tangybbq/keyboard/mesa2/thumb-1to1.pdf

## mesa2 - thumb angle and reach, LEFT hand, hand-local

100.0 mm - print at 100%, no fit-to-page

Within a row only the ANGLE of the line through the two thumb keys changes.
Between rows only the REACH changes. The index column is redrawn in each cell so the distance from finger to thumb is identical across a row - register your index on it every time. Lay the thumb across a pair: the right one is reached without moving the wrist and lands square on both keys. If none fits, use measure-blank.svg - sweep and tap 4-5 dots on the arc.

### reach as V1

-15 deg | +0 deg | +15 deg

### reach 8 mm further from the fingers

-15 deg | +0 deg | +15 deg
