tangybbq/keyboard/mesa2/variants-1to1.pdf

## mesa2 - finger variants, LEFT hand, hand-local (unibody angle removed)

100.0 mm - print at 100%, no fit-to-page

Columns are anchored and splayed about their CENTRE - the point the finger rests on between the two keys - not about either key. Rest a finger on the ridge between a column's two caps. Both are chouchou with your corrections applied, bracketing the amount: spread down, pinky and index staggered toward the palm, pinky rotated harder. 1u caps. Thumb pairs are placeholders -
use thumb-1to1 for those. You already have chouchou printed; compare against that.

### V1 modest spread 19.0/19.5/21.0 stagger 24.0/6.8/0/12.0 splay +21/+5/0/-5 rock 17

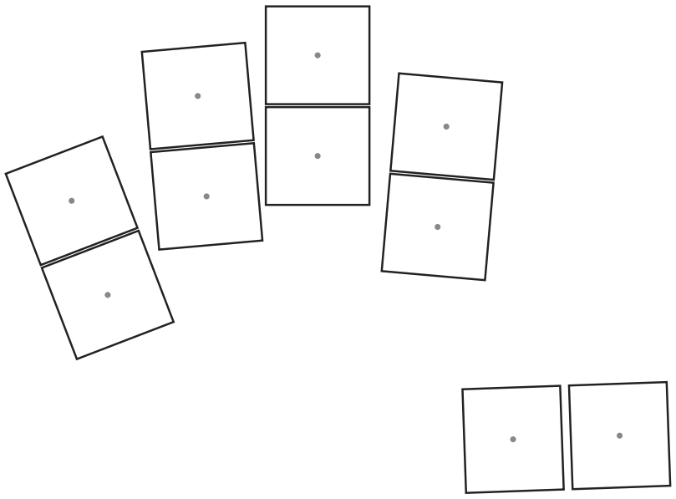
[picture p5: figure]

### V2 stronger spread 18.0/19.2/19.5 stagger 27.0/7.0/0/15.0 splay +26/+6/0/-6 rock 17

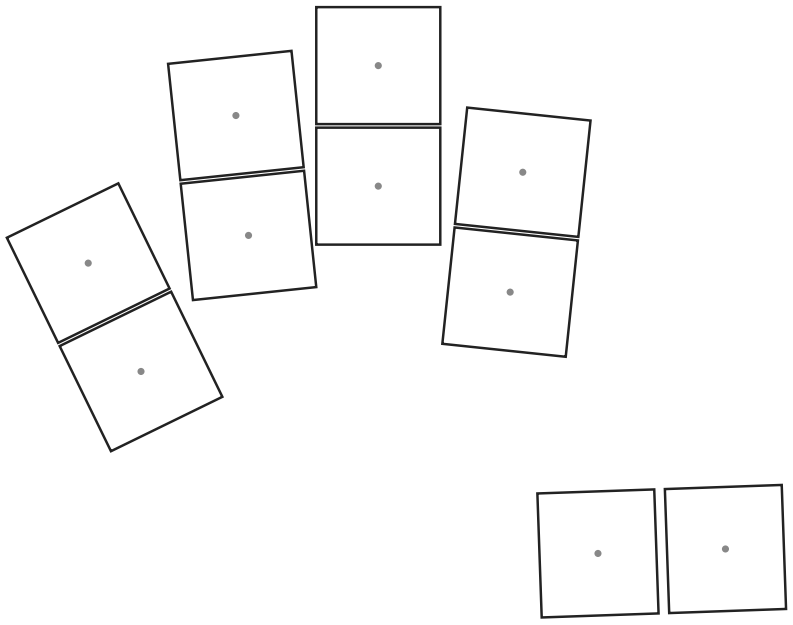
[picture p6: figure]
