tangybbq/keyboard/mesa2/hand-scan-1.pdf

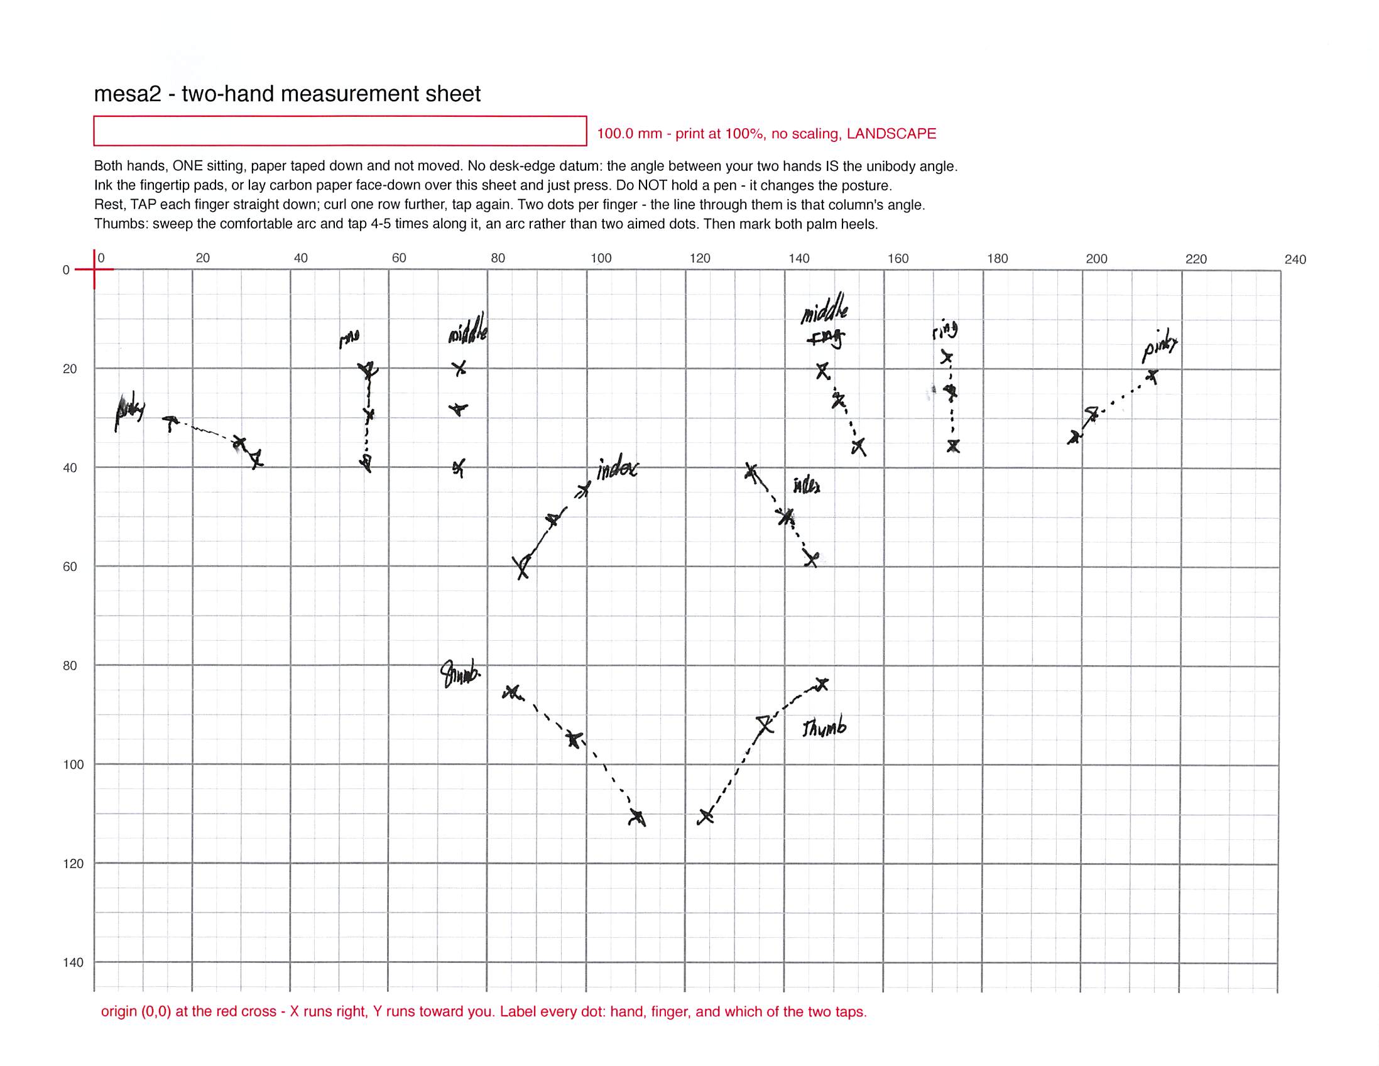
[picture p7: page 1]
