tangybbq/keyboard/bleproto.png

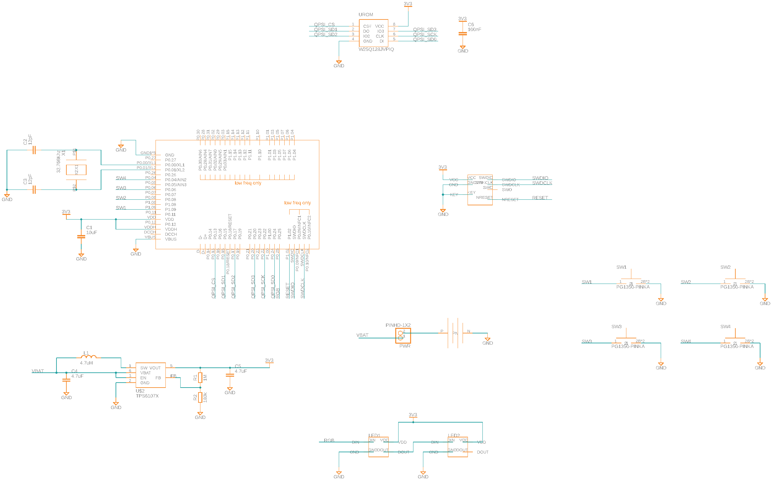
bleproto.png
