tangybbq/keyboard/img/my-qwerty.drawio.png

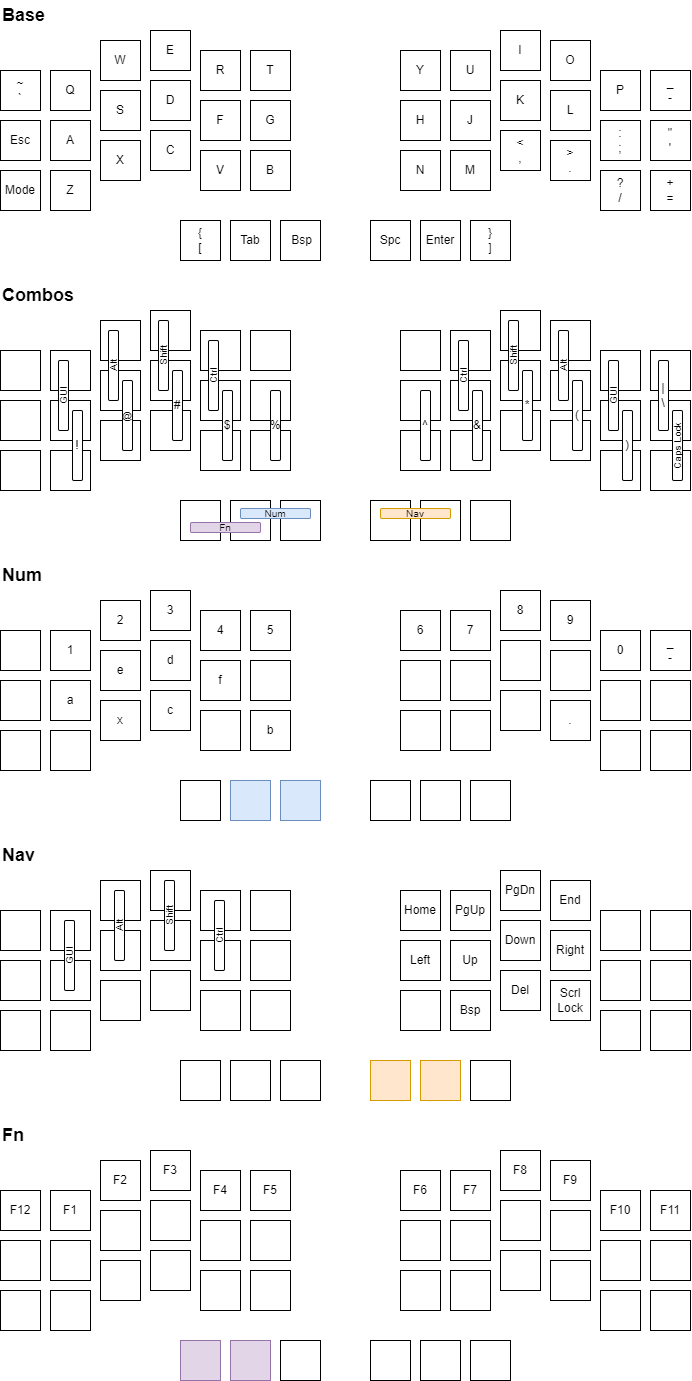
img/my-qwerty.drawio.png
