tangybbq/keyboard/inventory/DK_PRODUCTS_84602158.csv

Index | DigiKey Part # | Manufacturer Part Number | Description | Customer Reference | Quantity | Backorder | Unit Price | Extended Price
1 | USB-TMS2-M01-X-ND | USB-TMS2-M01-X | PROTOCOL ANALYZER USB DEVICES |  | 1 | 0 | $1,152.01000 | $1,152.01
 |  |  |  |  |  |  | Subtotal | $1,152.01
