tangybbq/keyboard/inventory/DK_PRODUCTS_88064886.csv

Index | DigiKey Part # | Manufacturer Part Number | Description | Customer Reference | Quantity | Backorder | Unit Price | Extended Price
1 | W25Q128JVPIQ-ND | W25Q128JVPIQ | IC FLASH 128MBIT SPI/QUAD 8WSON |  | 4 | 0 | $1.18000 | $4.72
2 | 2151-RT3215-32.768-9-TRCT-ND | RT3215-32.768-9-TR | CRYSTAL 32.7680KHZ 9PF SMD |  | 4 | 0 | $0.47000 | $1.88
3 | 296-17151-1-ND | TPS61070DDCR | IC REG BOOST ADJ 500MA SOT23 |  | 4 | 0 | $1.16000 | $4.64
4 | 1528-2827-ND | 4048 | CONN HEADER SMD 10POS 1.27MM |  | 4 | 0 | $1.95000 | $7.80
5 | 587-2527-1-ND | CB2012T4R7M | FIXED IND 4.7UH 580MA 520MOHM SM |  | 10 | 0 | $0.16800 | $1.68
6 | A119955CT-ND | CPF0603B1M0E | RES SMD 1M OHM 0.1% 1/16W 0603 |  | 10 | 0 | $0.15500 | $1.55
7 | P180KDBCT-ND | ERA-3AEB184V | RES SMD 180K OHM 0.1% 1/10W 0603 |  | 10 | 0 | $0.09800 | $0.98
8 | 1276-1119-1-ND | CL10A106MQ8NNNC | CAP CER 10UF 6.3V X5R 0603 |  | 10 | 0 | $0.07900 | $0.79
9 | 478-KGM15ACG2A120JMCT-ND | KGM15ACG2A120JM | CAP CER 12PF 100V C0G/NP0 0603 |  | 10 | 0 | $0.06000 | $0.60
10 | 1276-1044-1-ND | CL10A475KP8NNNC | CAP CER 4.7UF 10V X5R 0603 |  | 10 | 0 | $0.04100 | $0.41
11 | 311-1088-1-ND | CC0603KRX7R7BB104 | CAP CER 0.1UF 16V X7R 0603 |  | 10 | 0 | $0.04200 | $0.42
 |  |  |  |  |  |  | Subtotal | $25.47
