tangybbq/keyboard/inventory/DK_PRODUCTS_89321265.csv

Index | DigiKey Part # | Manufacturer Part Number | Description | Customer Reference | Quantity | Backorder | Unit Price | Extended Price
1 | 1490-NRF-PPK2-ND | NRF-PPK2 | POWER PROFILER KIT |  | 1 | 0 | $89.00000 | $89.00
 |  |  |  |  |  |  | Subtotal | $89.00
