tangybbq/keyboard/inventory/DK_PRODUCTS_89958897.csv

Index | DigiKey Part # | Manufacturer Part Number | Description | Customer Reference | Quantity | Backorder | Unit Price | Extended Price
1 | 1490-NRF5340-DK-ND | NRF5340-DK | DEV KIT FOR NRF5340 |  | 1 | 0 | $49.00000 | $49.00
2 | 587-2045-1-ND | LBR2012T100K | FIXED IND 10UH 150MA 360MOHM SMD |  | 25 | 0 | $0.07960 | $1.99
3 | MAX40200AUK+TCT-ND | MAX40200AUK+T | IC DIODE CURRENT SWITCH SOT23-5 |  | 10 | 0 | $1.07500 | $10.75
4 | P2.2GCT-ND | ERJ-3GEYJ2R2V | RES SMD 2.2 OHM 5% 1/10W 0603 |  | 10 | 0 | $0.03200 | $0.32
 |  |  |  |  |  |  | Subtotal | $62.06
