tangybbq/keyboard/bletest-2/bom-reva.xlsx

Reference | Value | Qty | Datasheet | Footprint | DNP
BT1 | Battery | 1 | ~ | davidb-keyboard-foot:BAT-2xAA-SHELL-CASE-BOX-NOSCREW
C1,C2,C3,C6 | 4.7uF | 4 | ~ | Capacitor_SMD:C_0603_1608Metric
C4,C5 | 1uF | 2 | ~ | Capacitor_SMD:C_0603_1608Metric
C7 | 100nF | 1 | ~ | Capacitor_SMD:C_0603_1608Metric
D1,D2,D3,D4,D5 | BAV19W | 5 | ~ | Diode_SMD:Nexperia_CFP3_SOD-123W
D6,D7 | SK6812MINI | 2 | https://cdn-shop.adafruit.com/product-files/2686/SK6812MINI_REV.01-1-2.pdf | LED_SMD:LED_SK6812MINI_PLCC4_3.5x3.5mm_P1.75mm
J-LEFT1,J-RIGHT1 | RJ45 | 2 | ~ | Connector_RJ:RJ45_Amphenol_54602-x08_Horizontal
J1,J2,J4,J5,J6,J8 | Conn_01x02 | 6 | ~ | Connector_PinHeader_2.54mm:PinHeader_1x02_P2.54mm_Vertical
J3 | Conn_ARM_JTAG_SWD_10 | 1 | http://infocenter.arm.com/help/topic/com.arm.doc.ddi0314h/DDI0314H_coresight_components_trm.pdf | davidb-keyboard-foot:Cortex-M-Debug10
J7 | USB_C_Receptacle_USB2.0_16P | 1 | https://www.usb.org/sites/default/files/documents/usb_type-c.zip | Connector_USB:USB_C_Receptacle_GCT_USB4085
L1 | 4.7uH | 1 | ~ | Inductor_SMD:L_0805_2012Metric
L2,L3 | 10uH | 2 | ~ | Inductor_SMD:L_0805_2012Metric
R1 | 1M | 1 | ~ | Resistor_SMD:R_0603_1608Metric
R2,R8 | 180K | 2 | ~ | Resistor_SMD:R_0603_1608Metric
R3,R4,R5 | 5.1K | 3 | ~ | Resistor_SMD:R_0603_1608Metric
R6,R7 | 2.2 | 2 | ~ | Resistor_SMD:R_0603_1608Metric
SW1,SW2,SW3,SW4 | SW_Push | 4 | ~ | Keyboard Switches:Kailh_socket_PG1350
U1 | MAX40200AUK | 1 | https://datasheets.maximintegrated.com/en/ds/MAX40200.pdf | Package_TO_SOT_SMD:SOT-23-5
U2,U3 | ~ | 2 |  | -- mixed values --
U4 | W25Q128JVP | 1 | https://www.winbond.com/resource-files/w25q128jv_dtr%20revc%2003272018%20plus.pdf | Package_SON:WSON-8-1EP_6x5mm_P1.27mm_EP3.4x4.3mm
Y1 | Crystal | 1 | ~ | Crystal:Crystal_SMD_3215-2Pin_3.2x1.5mm
