tangybbq/keyboard/mesa3/mesa3-left/production/bom.csv

Designator | Footprint | Quantity | Value | LCSC Part #
A1 | Pimoroni_Tiny2040 | 1 | Pimoroni_Tiny2040
C1, C2, C3, C4 | 0603 | 4 | 100nF
D1, D_LA1, D_LBK1, D_LE1, D_LFN1, D_LI1, D_LN1, D_LO1, D_LS1, D_LSP1, D_LT1 | D_SOD-123 | 11 | 1N4148W
J1 | RJ45_Amphenol_54602-x08_Horizontal | 1 | RJ45
J2 | Tag-Connect_TC2030-IDC-FP_2x03_P1.27mm_Vertical | 1 | Tag-Connect TC2030
LED1, LED2, LED3, LED4 | SK6812-MINI-HS | 4 | SK6812MINI-HS
RESET1 | TestPoint_Pad_2.0x2.0mm | 1 | RESET_WIRE
SW_LA1, SW_LBK1, SW_LE1, SW_LFN1, SW_LI1, SW_LN1, SW_LO1, SW_LS1, SW_LSP1, SW_LT1 | Kailh_socket_PG1350 | 10 | SW_PG1350
