tangybbq/keyboard/mesa3/mesa3-right/production/bom.csv

Designator | Footprint | Quantity | Value | LCSC Part #
D_RA1, D_RBK1, D_RE1, D_RFN1, D_RI1, D_RN1, D_RO1, D_RS1, D_RSP1, D_RT1 | D_SOD-123 | 10 | 1N4148W
J1 | RJ45_Amphenol_54602-x08_Horizontal | 1 | RJ45
SW_RA1, SW_RBK1, SW_RE1, SW_RFN1, SW_RI1, SW_RN1, SW_RO1, SW_RS1, SW_RSP1, SW_RT1 | Kailh_socket_PG1350 | 10 | SW_PG1350
