tangybbq/keyboard/mesa2/mesa2x/production/bom.csv

Designator | Footprint | Quantity | Value | LCSC Part #
A1 | Pimoroni_Tiny2040 | 1 | Pimoroni_Tiny2040
D_LA1, D_LBK1, D_LE1, D_LI1, D_LN1, D_LO1, D_LR1, D_LS1, D_LSP1, D_LT1, D_RA1, D_RBK1, D_RE1, D_RI1, D_RN1, D_RO1, D_RR1, D_RS1, D_RSP1, D_RT1 | D_SOD-123 | 20 | 1N4148W
J2 | Tag-Connect_TC2030-IDC-FP_2x03_P1.27mm_Vertical | 1 | Tag-Connect TC2030
LED1, LED2, LED3, LED4 | SK6812-MINI-HS | 4 | SK6812MINI-HS
RESET1 | TestPoint_Pad_2.0x2.0mm | 1 | RESET_WIRE
SW_LA1, SW_LBK1, SW_LE1, SW_LI1, SW_LN1, SW_LO1, SW_LR1, SW_LS1, SW_LSP1, SW_LT1, SW_RA1, SW_RBK1, SW_RE1, SW_RI1, SW_RN1, SW_RO1, SW_RR1, SW_RS1, SW_RSP1, SW_RT1 | Kailh_socket_PG1350 | 20 | SW_PG1350
