tangybbq/keyboard/mesa1/mesa1-right/production/bom.csv

Designator | Footprint | Quantity | Value | LCSC Part #
D_RB0, D_RD0, D_RE0, D_RF0, D_RG0, D_RL0, D_RNUM0, D_RP0, D_RR0, D_RS3, D_RS4, D_RT0, D_RU0, D_RZ0, D_TS0 | D_SOD-123 | 15 | 1N4148W
J1 | RJ45_Amphenol_54602-x08_Horizontal | 1 | RJ45
RB0, RD0, RE0, RF0, RG0, RL0, RNUM0, RP0, RR0, RS3, RS4, RT0, RU0, RZ0, TS0 | Kailh_socket_PG1350 | 15 | SW_PG1350
