tangybbq/keyboard/inventory/DK_PRODUCTS_85531273.csv

Index | DigiKey Part # | Manufacturer Part Number | Description | Customer Reference | Quantity | Backorder | Unit Price | Extended Price
1 | 1778-PIM558-ND | PIM558 | TINY 2040 |  | 5 | 0 | $9.70000 | $48.50
 |  |  |  |  |  |  | Subtotal | $48.50
