tangybbq/keyboard/inventory/DK_PRODUCTS_89091843.csv

Index | DigiKey Part # | Manufacturer Part Number | Description | Customer Reference | Quantity | Backorder | Unit Price | Extended Price
1 | 1778-PIM558-ND | PIM558 | TINY 2040 |  | 6 | 0 | $9.70000 | $58.20
2 | 1528-2827-ND | 4048 | CONN HEADER SMD 10POS 1.27MM |  | 10 | 0 | $1.95000 | $19.50
3 | 609-5081-ND | 54601-908WPLF | CONN MOD JACK 8P8C R/A UNSHLD |  | 30 | 0 | $0.32600 | $9.78
 |  |  |  |  |  |  | Subtotal | $87.48
