tangybbq/keyboard/proto4/proto4-left/dxf/proto4-left-Edge_Cuts.dxf

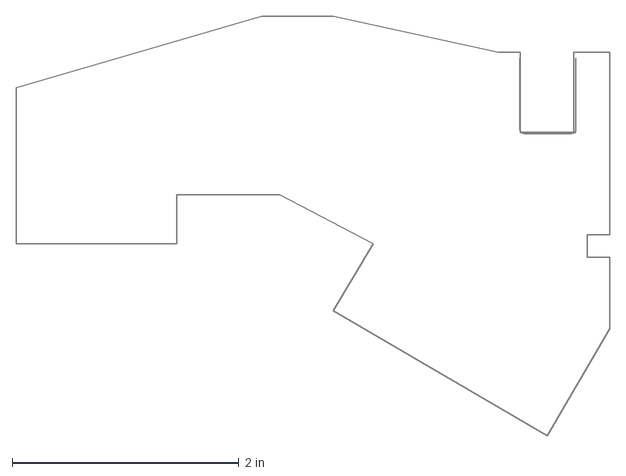
[picture p24: CAD file, 2026-09-14]
proto4/proto4-left/dxf/proto4-left-Edge_Cuts.dxf
5.24 x 3.70 in
