tangybbq/keyboard/proto4/proto4-left/proto4-left.step

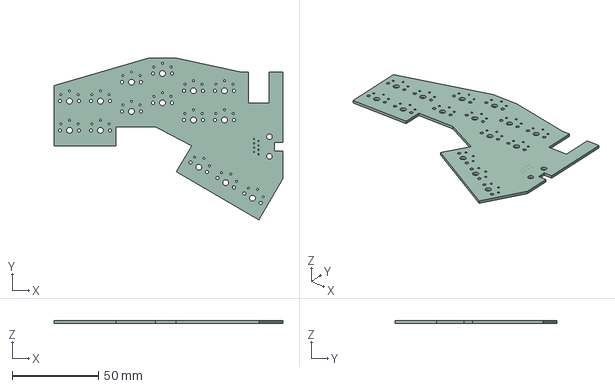
[picture p25: CAD file, 2026-09-14]
proto4/proto4-left/proto4-left.step
133.0 x 94.0 x 1.51 mm
