tangybbq/keyboard/Top-jolt1.3mf

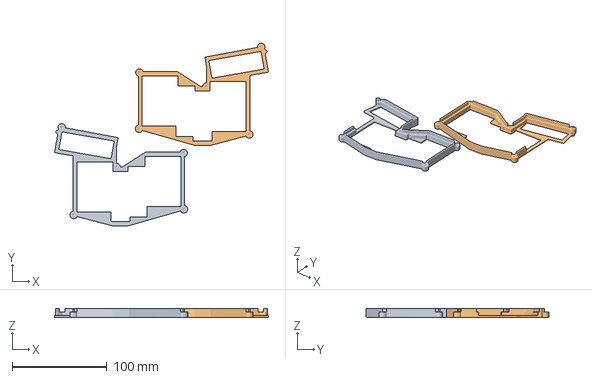
[picture p26: CAD file, 2026-09-14]
Top-jolt1.3mf
226.2 x 193.1 x 9.80 mm
Top x 2
