tangybbq/keyboard/BasePlate-jolt1.3mf

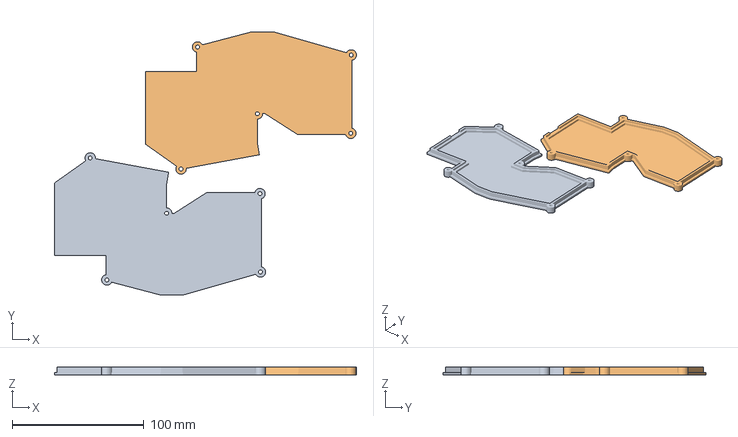
[picture p27: CAD file, 2026-09-14]
BasePlate-jolt1.3mf
229.2 x 199.7 x 6.00 mm
BasePlate x 2
