tangybbq/keyboard/jolt2/empty-outline/empty-outline.step

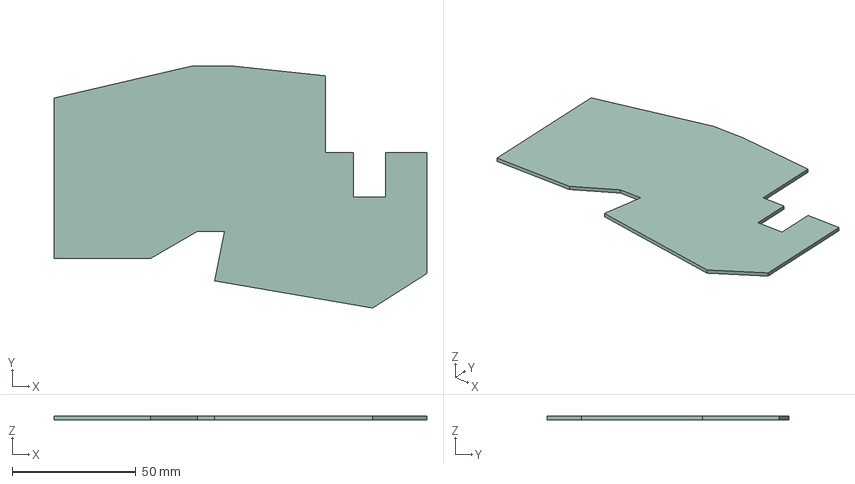
[picture p28: CAD file, 2025-01-04]
jolt2/empty-outline/empty-outline.step
151.0 x 98.0 x 1.60 mm
