tangybbq/keyboard/jolt2/jolt2-tiny2040-left/board-case.FCStd

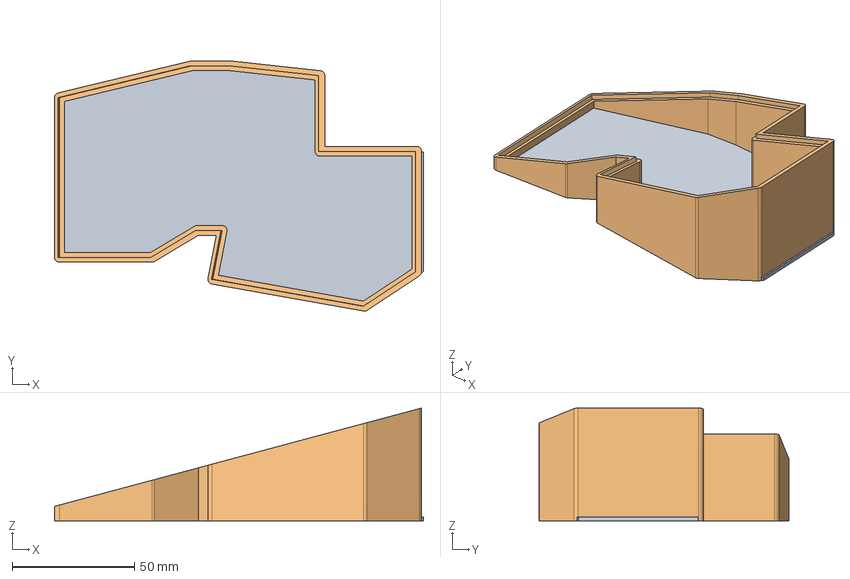
[picture p29: CAD file, 2025-01-04]
jolt2/jolt2-tiny2040-left/board-case.FCStd
151.0 x 102.4 x 46.2 mm
PCB
Base-obj
