tangybbq/keyboard/jolt2/jolty-2040/jolt-left.3mf

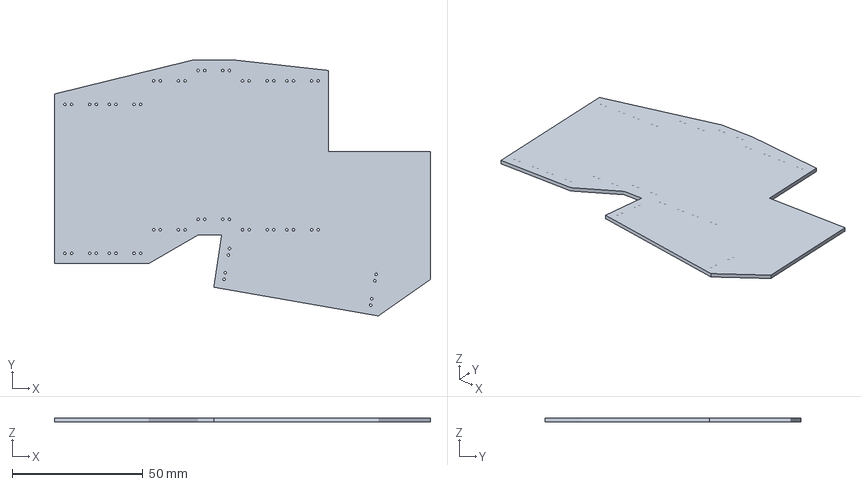
[picture p30: CAD file, 2024-12-16]
jolt2/jolty-2040/jolt-left.3mf
144.0 x 98.0 x 1.60 mm
