tangybbq/keyboard/mesa1/3dmodels/SW_Kailh_Choc_V1.step

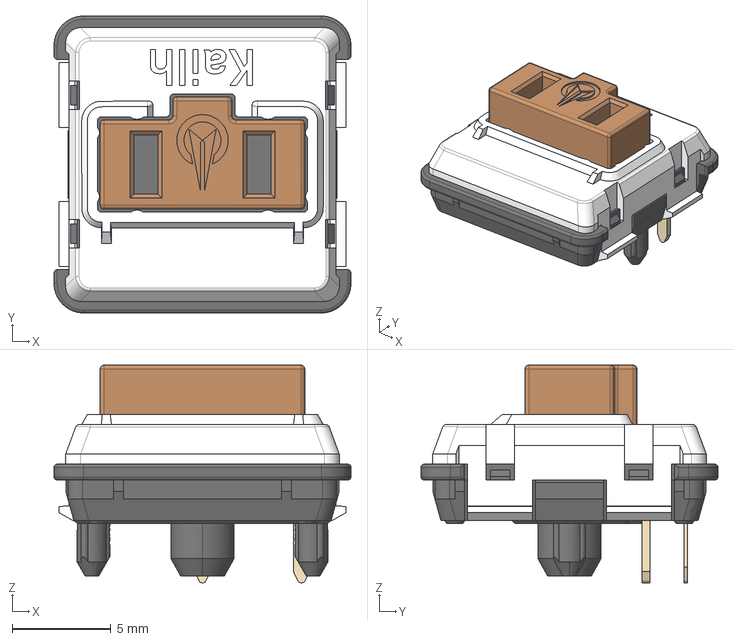
[picture p31: CAD file, 2026-08-15]
mesa1/3dmodels/SW_Kailh_Choc_V1.step
15.0 x 15.0 x 11.0 mm
