tangybbq/keyboard/mesa1/mesa1-left-Edge_Cuts.dxf

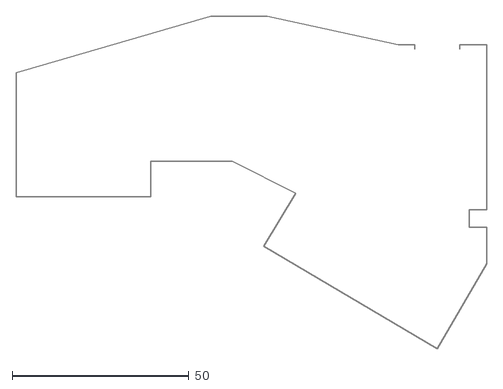
[picture p32: CAD file, 2026-08-09]
mesa1/mesa1-left-Edge_Cuts.dxf
133.0 x 94.0
