tangybbq/keyboard/proto2/case-right-top.3mf

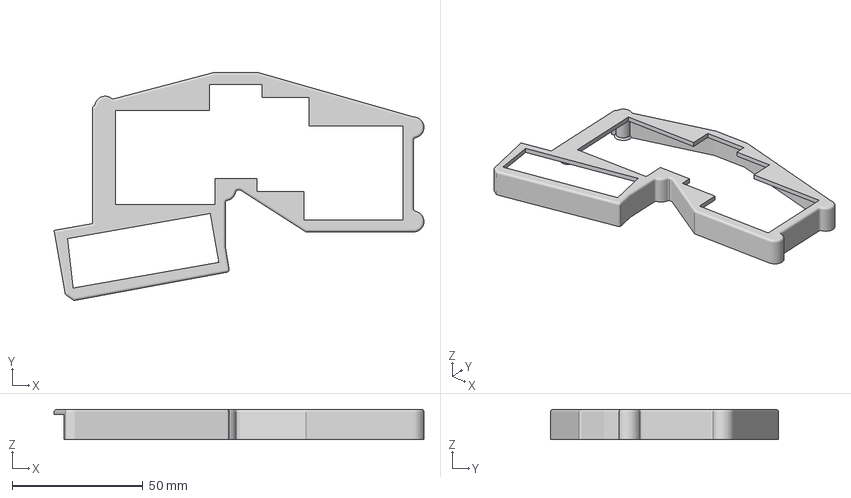
[picture p33: CAD file, 2022-10-30]
proto2/case-right-top.3mf
141.6 x 87.2 x 11.6 mm
