tangybbq/keyboard/BasePlate.3mf

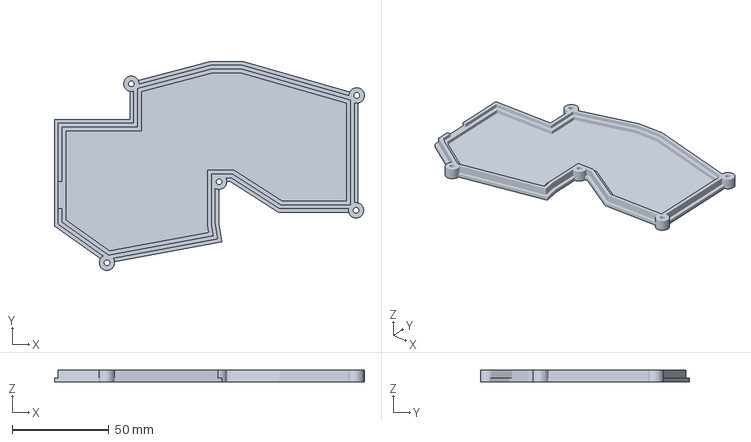
[picture p34: CAD file, 2026-09-14]
BasePlate.3mf
160.3 x 108.0 x 6.00 mm
