tangybbq/keyboard/jolt2/jolt2-tiny2040-left/board-case-Base-obj.3mf

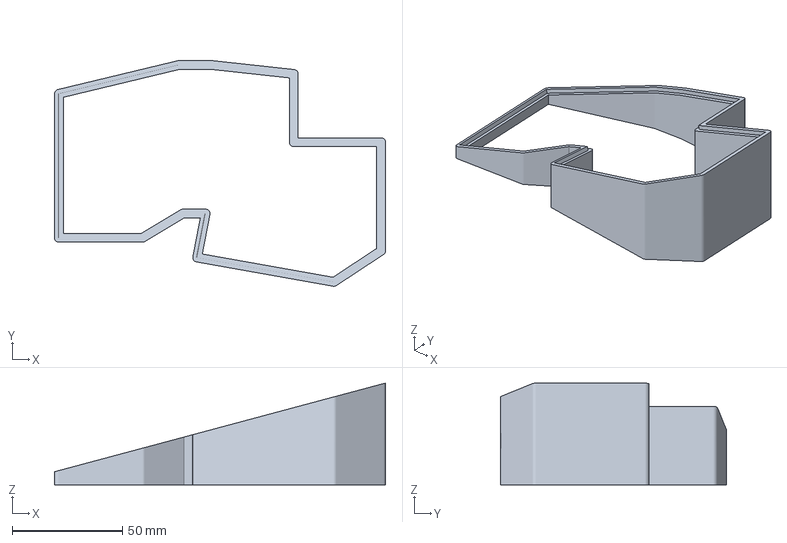
[picture p35: CAD file, 2025-01-04]
jolt2/jolt2-tiny2040-left/board-case-Base-obj.3mf
150.2 x 102.4 x 46.2 mm
