tangybbq/keyboard/jolt2/jolt2-verts/vert-spacers-Body-10mm.3mf

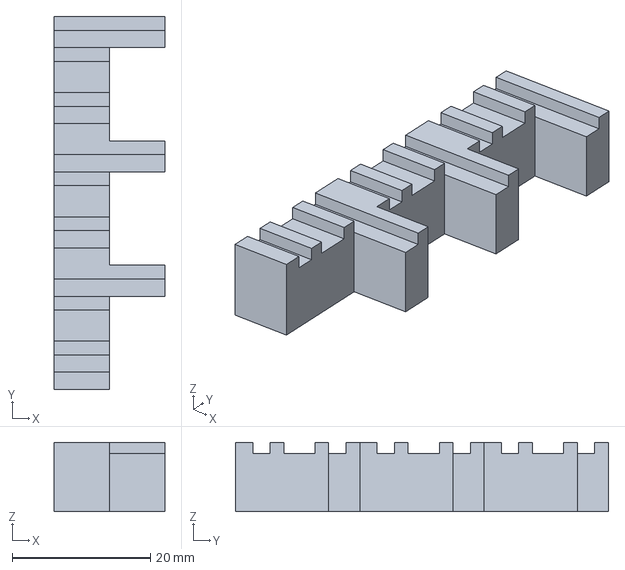
[picture p36: CAD file, 2025-01-04]
jolt2/jolt2-verts/vert-spacers-Body-10mm.3mf
16.0 x 54.0 x 10.0 mm
