tangybbq/keyboard/jolt2/jolty-2040/jolty-2040.step

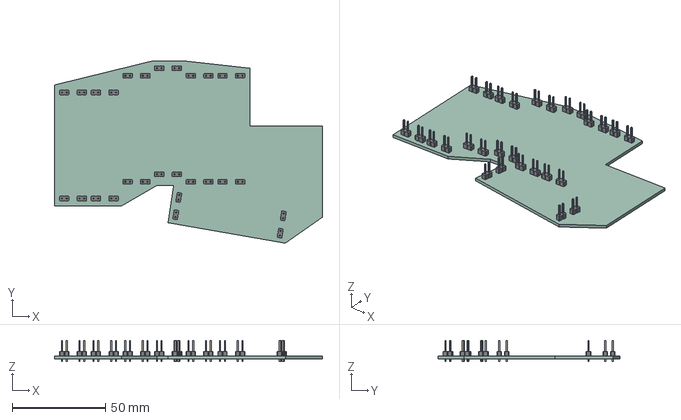
[picture p37: CAD file, 2024-12-16]
jolt2/jolty-2040/jolty-2040.step
144.0 x 98.0 x 11.5 mm
PinHeader_1x02_P254mm_Vertical x 28
jolt2-left_PCB
