tangybbq/keyboard/mesa1/3dmodels/MBK_Keycap_1u.step

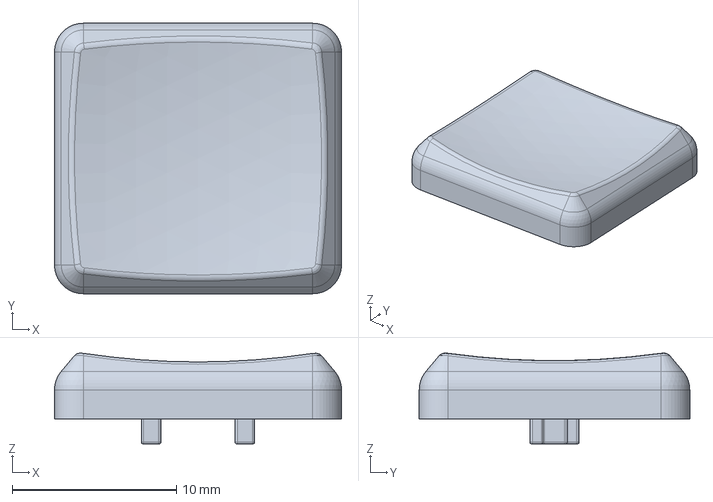
[picture p38: CAD file, 2026-08-15]
mesa1/3dmodels/MBK_Keycap_1u.step
17.4 x 16.4 x 5.52 mm
