tangybbq/keyboard/jolt2/jolt2-verts/jolt2-verts.step

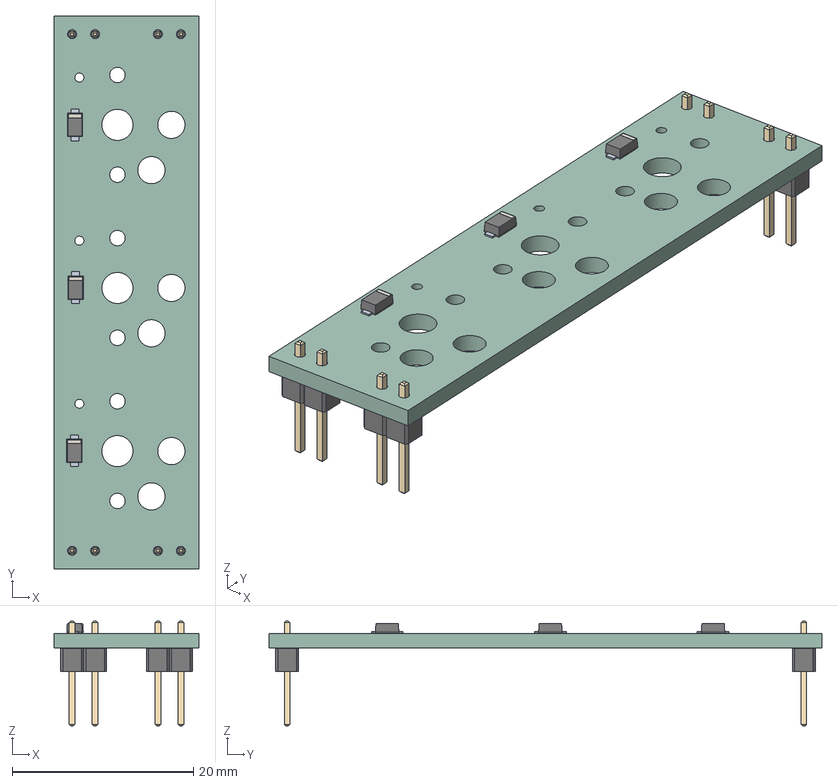
[picture p39: CAD file, 2025-01-04]
jolt2/jolt2-verts/jolt2-verts.step
16.0 x 61.0 x 11.5 mm
CQ assembly x 3
PinHeader_1x02_P254mm_Vertical x 4
jolt2-verts_PCB
