tangybbq/keyboard/mesa1/3dmodels/Kailh_socket_PG1350.step

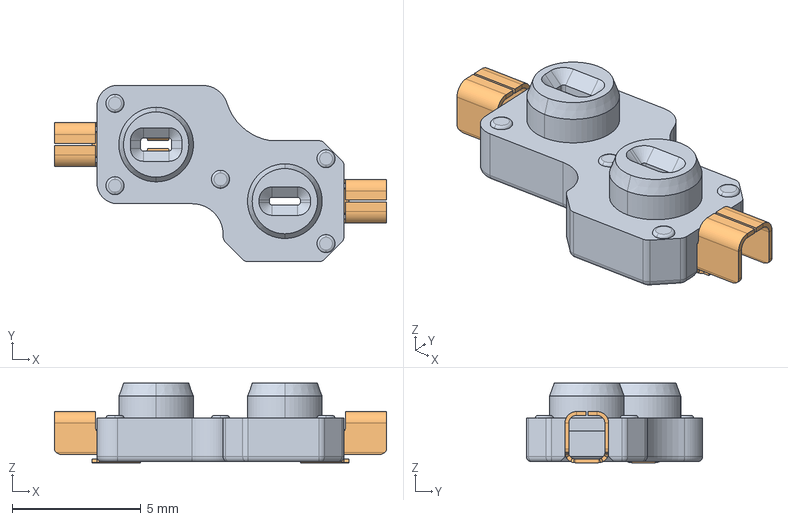
[picture p40: CAD file, 2026-08-15]
mesa1/3dmodels/Kailh_socket_PG1350.step
12.9 x 6.85 x 3.09 mm
socket001
pin002
pin003
