tangybbq/keyboard/jolt2/jolty-2040/jolt2-verts-jolt2-verts 1jolt2-verts_PCB.3mf

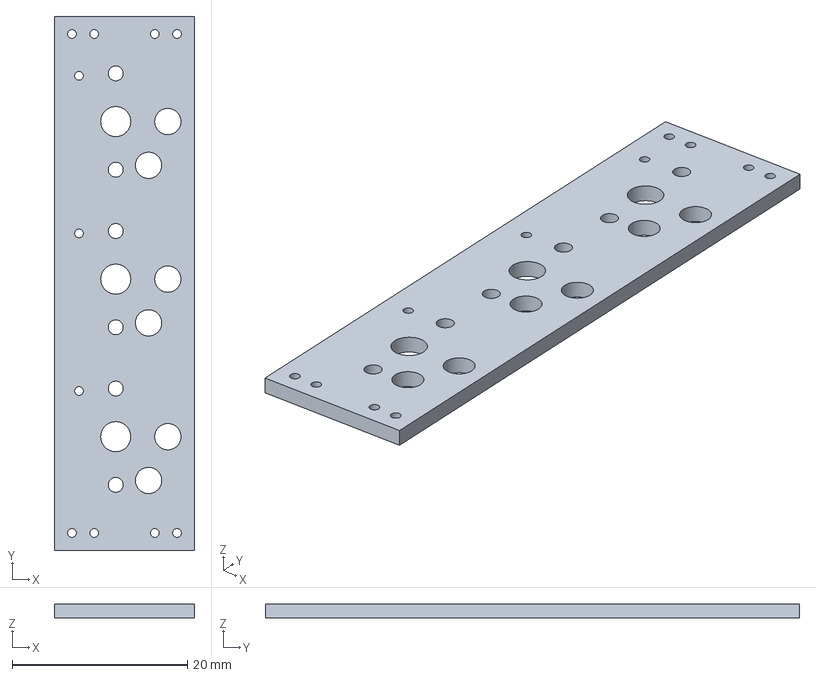
[picture p41: CAD file, 2024-12-16]
jolt2/jolty-2040/jolt2-verts-jolt2-verts 1jolt2-verts_PCB.3mf
16.0 x 61.0 x 1.60 mm
