tangybbq/keyboard/mesa1/3dmodels/RJ45_Amphenol_54602-x08_Horizontal.step

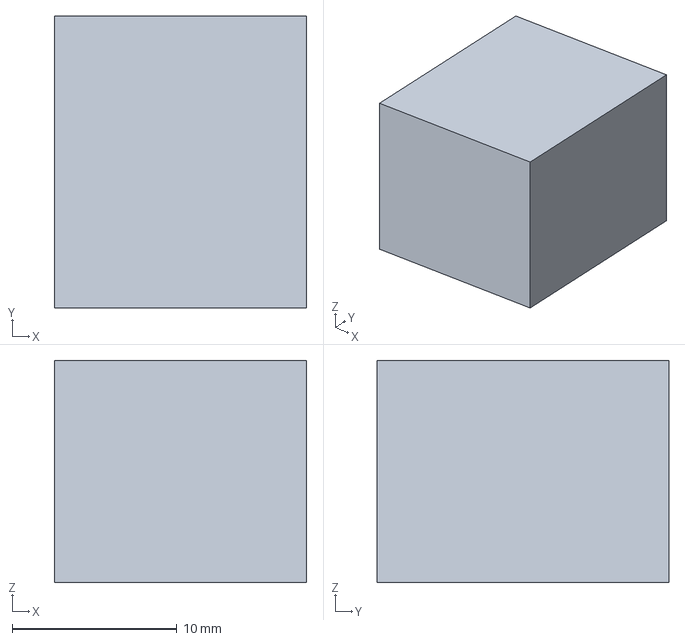
[picture p42: CAD file, 2026-08-09]
mesa1/3dmodels/RJ45_Amphenol_54602-x08_Horizontal.step
15.3 x 17.7 x 13.5 mm
