tangybbq/keyboard/jolt2/jolt2-verts/kailhlowsocket01.stl

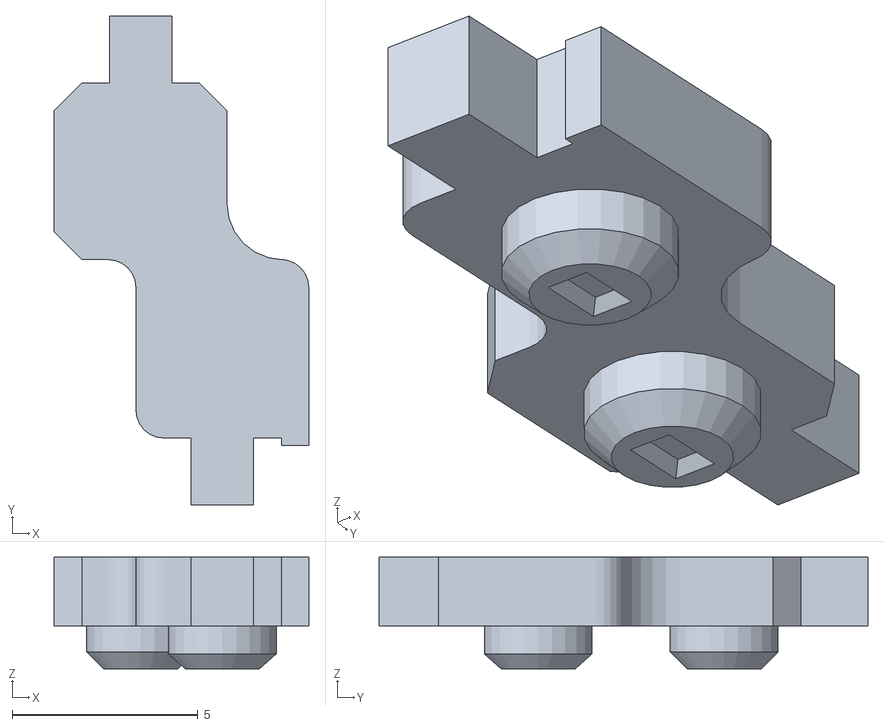
[picture p43: CAD file, 2025-01-04]
jolt2/jolt2-verts/kailhlowsocket01.stl
6.85 x 13.2 x 3.00
