tangybbq/keyboard/jolt2/jolty-2040/pcb-jolt2-left 1jolt2-left_PCB.3mf

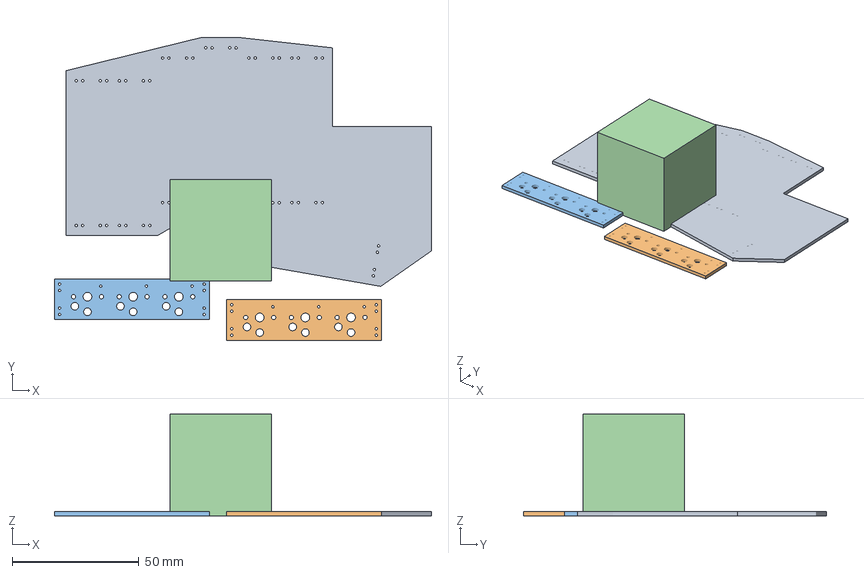
[picture p44: CAD file, 2024-12-16]
jolt2/jolty-2040/pcb-jolt2-left 1jolt2-left_PCB.3mf
148.6 x 119.2 x 40.0 mm
pcb-jolt2-left 1jolt2-left_PCB
jolt2-verts-jolt2-verts 1jolt2-verts_PCB
cube-40-40-40.stl
