tangybbq/keyboard/jolt2/jolt2-verts/kailhlowprofilev102.stl

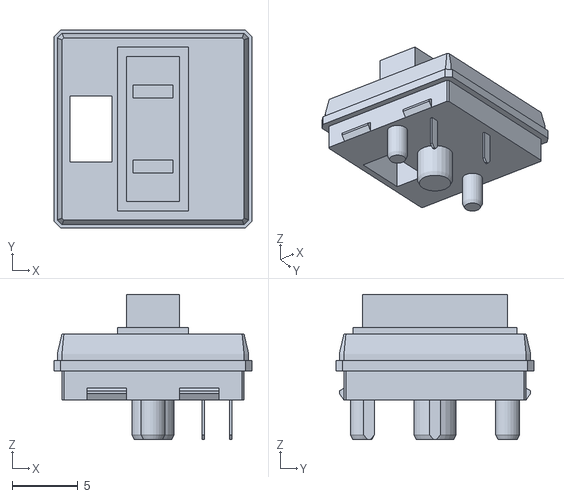
[picture p45: CAD file, 2025-01-04]
jolt2/jolt2-verts/kailhlowprofilev102.stl
15.0 x 15.0 x 11.0
