tangybbq/keyboard/jolt2/jolt2-verts/vert-spacers.FCStd

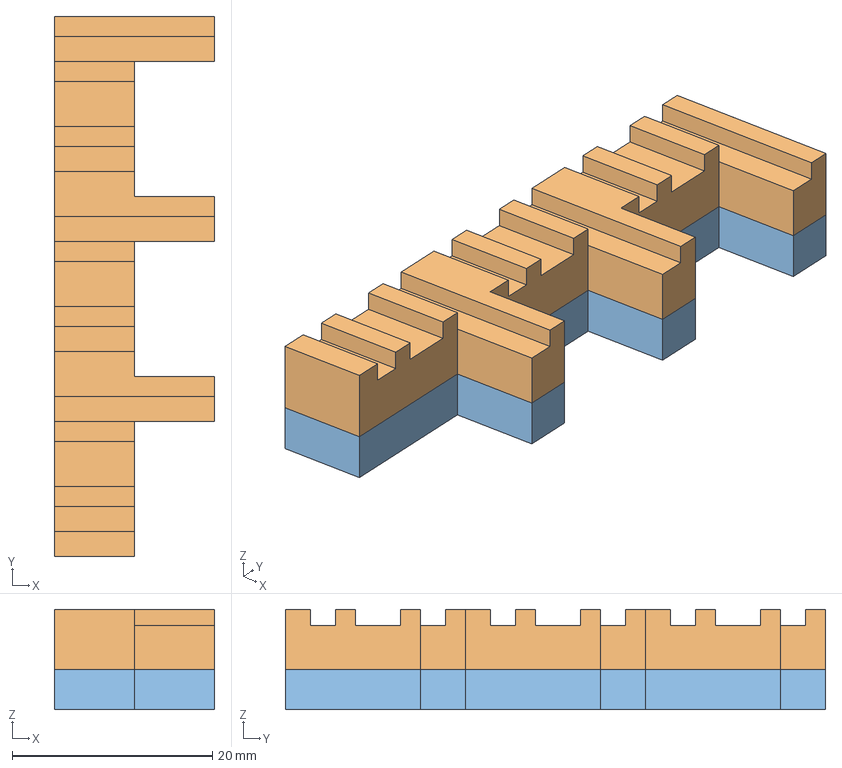
[picture p46: CAD file, 2025-01-04]
jolt2/jolt2-verts/vert-spacers.FCStd
16.0 x 54.0 x 10.0 mm
Body-4mm
Body-6mm
Body-10mm
