tangybbq/keyboard/jolt2/jolt2-verts/vert-spacers-Body-6mm.3mf

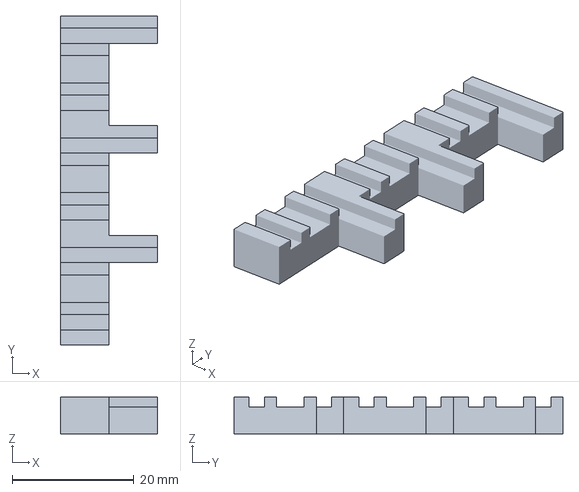
[picture p47: CAD file, 2025-01-04]
jolt2/jolt2-verts/vert-spacers-Body-6mm.3mf
16.0 x 54.0 x 6.00 mm
