tangybbq/keyboard/assembly/img/IMG_0325.jpeg

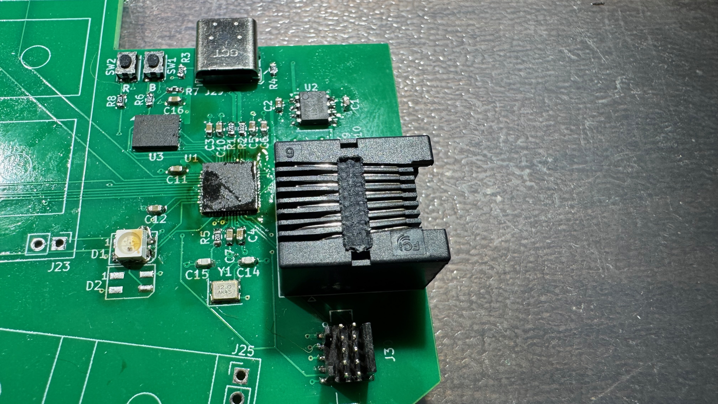
assembly/img/IMG_0325.jpeg
