tangybbq/keyboard/assembly/img/IMG_0329.jpeg

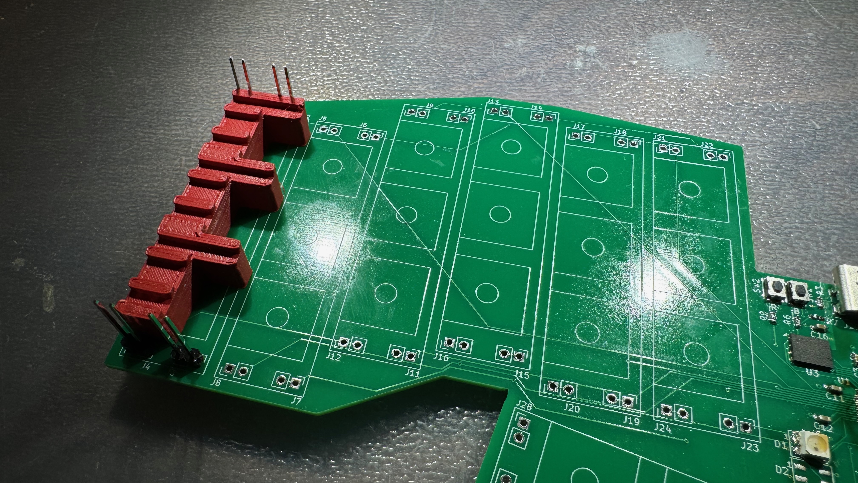
assembly/img/IMG_0329.jpeg
