tangybbq/keyboard/assembly/img/IMG_0333.jpeg

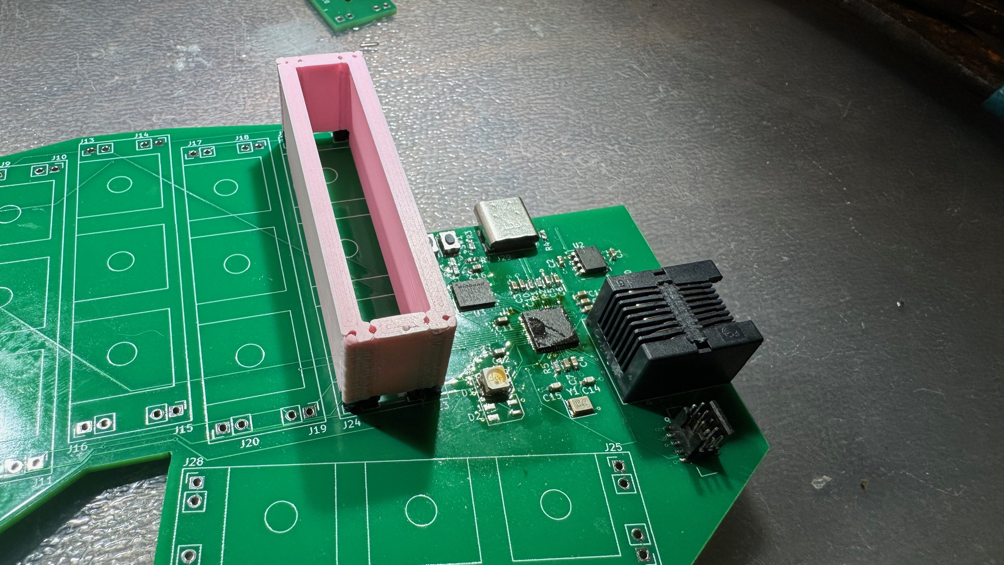
assembly/img/IMG_0333.jpeg
