tangybbq/keyboard/jolt2/jolt2-pm2350-left/jolt2-pm2350-left.kicad_pcb

## KiCad design jolt2/jolt2-pm2350-left/jolt2-pm2350-left.kicad_pcb (2024-12-17)

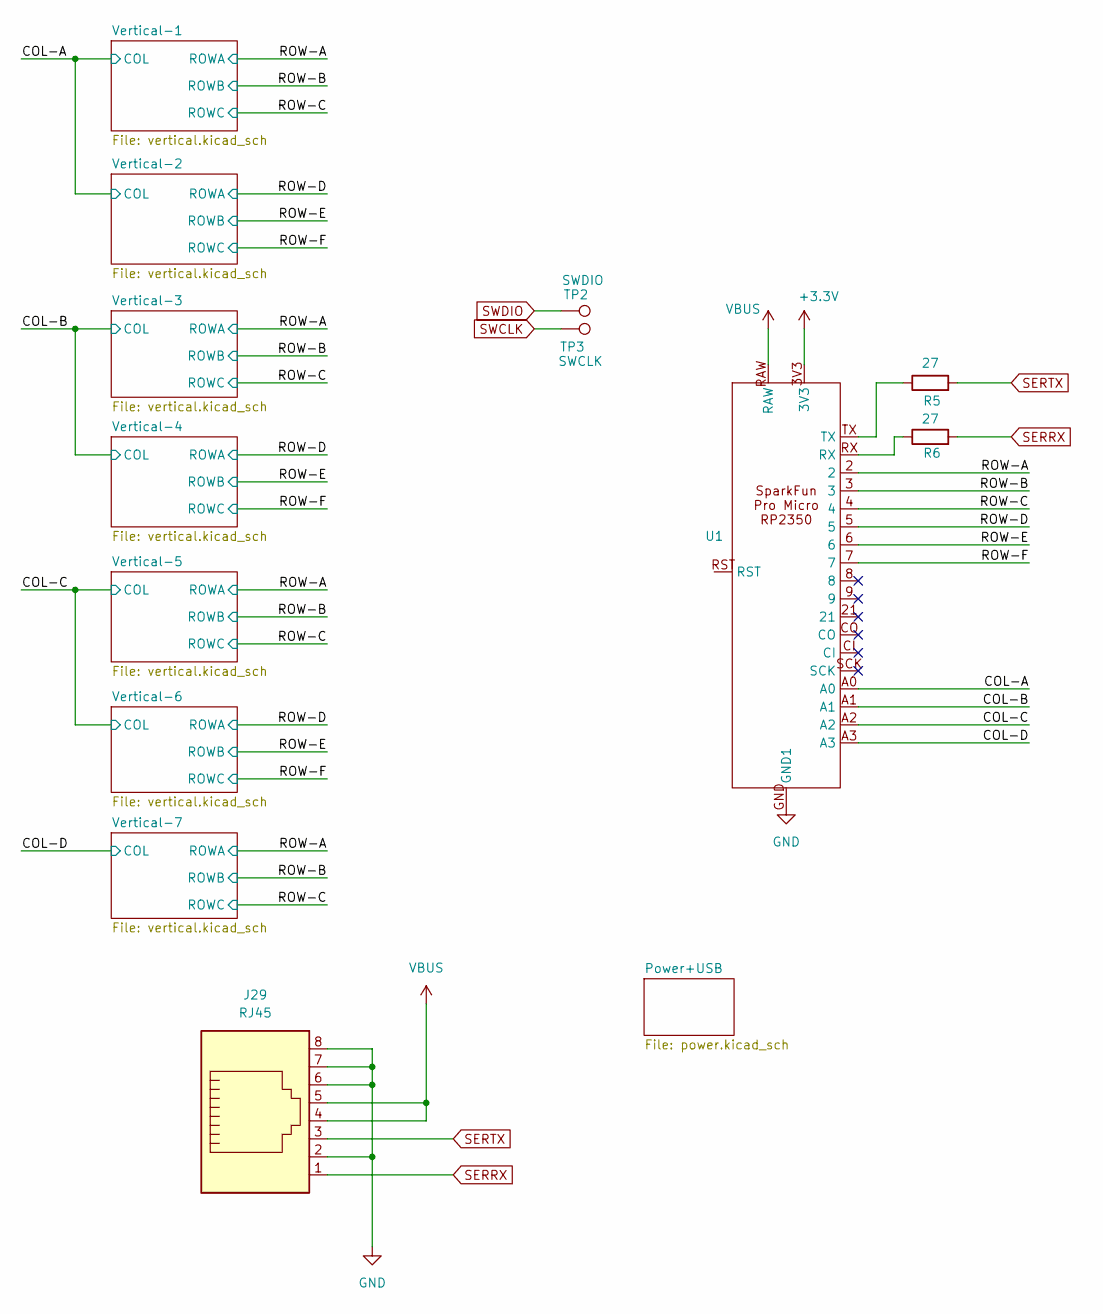
[picture p104: schematic jolt2-pm2350-left.kicad_sch, Jolt 2 - Left]

Parts:
J29: RJ45; RJ45_Amphenol_54602-x08_Horizontal
R5, R6: 27; R_0603_1608Metric_Pad0.98x0.95mm_HandSolder
TP2: SWDIO; TestPoint_Pad_1.5x1.5mm
TP3: SWCLK; TestPoint_Pad_1.5x1.5mm
U1: SparkFun_Pro_Micro_RP2350

Connections:
+3.3V: U1.3V3; also elsewhere on the board
/COL-A: U1.A0; also elsewhere on the board
/COL-B: U1.A1; also elsewhere on the board
/COL-C: U1.A2; also elsewhere on the board
/COL-D: U1.A3; also elsewhere on the board
/ROW-A: U1.2; also elsewhere on the board
/ROW-B: U1.3; also elsewhere on the board
/ROW-C: U1.4; also elsewhere on the board
/ROW-D: U1.5; also elsewhere on the board
/ROW-E: U1.6; also elsewhere on the board
/ROW-F: U1.7; also elsewhere on the board
GND: J29.2, J29.6, J29.7, J29.8, U1.GND (GND2); also elsewhere on the board
unnamed: R5.1, U1.TX
unnamed: R6.1, U1.RX
SERRX: J29.1, R6.2
SERTX: J29.3, R5.2
SWCLK: TP3.1; also elsewhere on the board
SWDIO: TP2.1; also elsewhere on the board
VBUS: J29.4, J29.5, U1.RAW

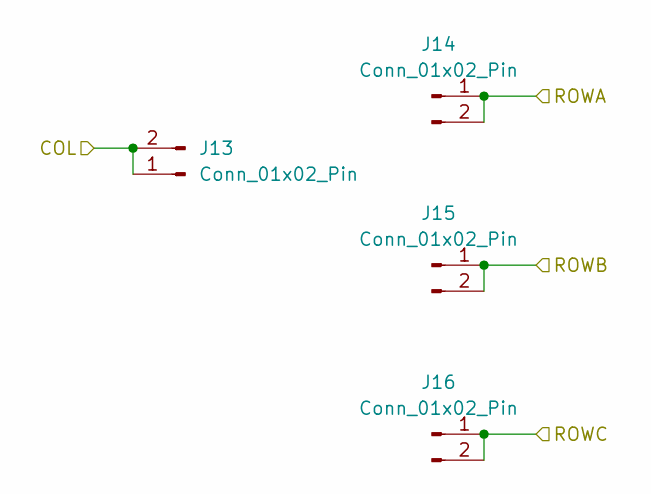
[picture p105: schematic vertical.kicad_sch]

Parts:
J13, J14, J15, J16: Conn_01x02_Pin; PinHeader_1x02_P2.54mm_Vertical

Connections:
/COL-B: J13.1, J13.2; also elsewhere on the board
/ROW-D: J14.1, J14.2; also elsewhere on the board
/ROW-E: J15.1, J15.2; also elsewhere on the board
/ROW-F: J16.1, J16.2; also elsewhere on the board

Parts of its further copies:
J1, J2, J3, J4, J5, J6, J7, J8, J9, J10, J11, J12, J17, J18, J19, J20, J21, J22, J23, J24, J25, J26, J27, J28: Conn_01x02_Pin; PinHeader_1x02_P2.54mm_Vertical

Connections of its further copies:
/COL-A: J1.1, J1.2, J5.1, J5.2; also elsewhere on the board
/COL-B: J9.1, J9.2; also elsewhere on the board
/COL-C: J17.1, J17.2, J21.1, J21.2; also elsewhere on the board
/COL-D: J25.1, J25.2; also elsewhere on the board
/ROW-A: J2.1, J2.2, J10.1, J10.2, J18.1, J18.2, J26.1, J26.2; also elsewhere on the board
/ROW-B: J3.1, J3.2, J11.1, J11.2, J19.1, J19.2, J27.1, J27.2; also elsewhere on the board
/ROW-C: J4.1, J4.2, J12.1, J12.2, J20.1, J20.2, J28.1, J28.2; also elsewhere on the board
/ROW-D: J6.1, J6.2, J22.1, J22.2; also elsewhere on the board
/ROW-E: J7.1, J7.2, J23.1, J23.2; also elsewhere on the board
/ROW-F: J8.1, J8.2, J24.1, J24.2; also elsewhere on the board

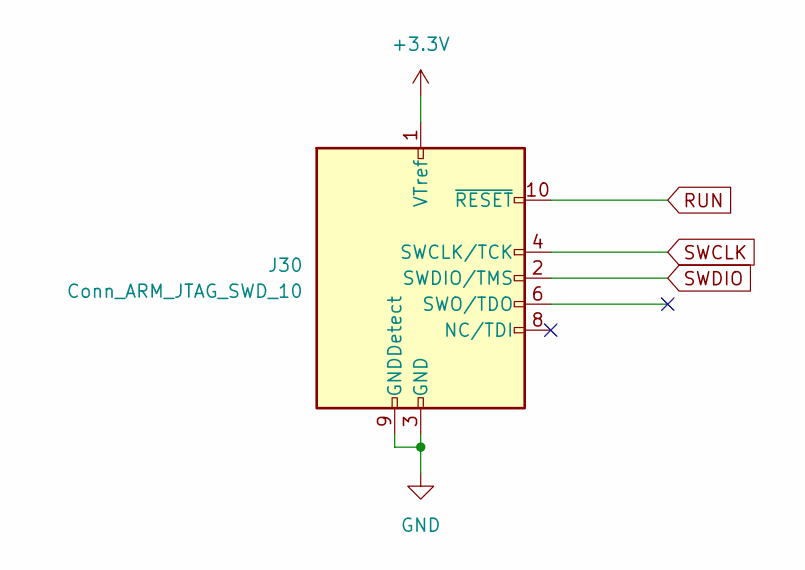
[picture p106: schematic power.kicad_sch, Jolt 2 - Left]

Parts:
J30: Conn_ARM_JTAG_SWD_10; Cortex-M-Debug10

Connections:
+3.3V: J30.1 (VTref); also elsewhere on the board
GND: J30.3 (GND), J30.5 (GND), J30.9 (GNDDetect); also elsewhere on the board
RUN: J30.10 (~RESET)
SWCLK: J30.4 (SWCLK/TCK); also elsewhere on the board
SWDIO: J30.2 (SWDIO/TMS); also elsewhere on the board

Board: 2 copper layers, 35 parts (2 on the bottom side), 19 nets, no tracks yet.
