tangybbq/keyboard/jolt2/jolt2-pim-left/jolt2-pim-left.kicad_pcb

## KiCad design jolt2/jolt2-pim-left/jolt2-pim-left.kicad_pcb (2024-12-16)

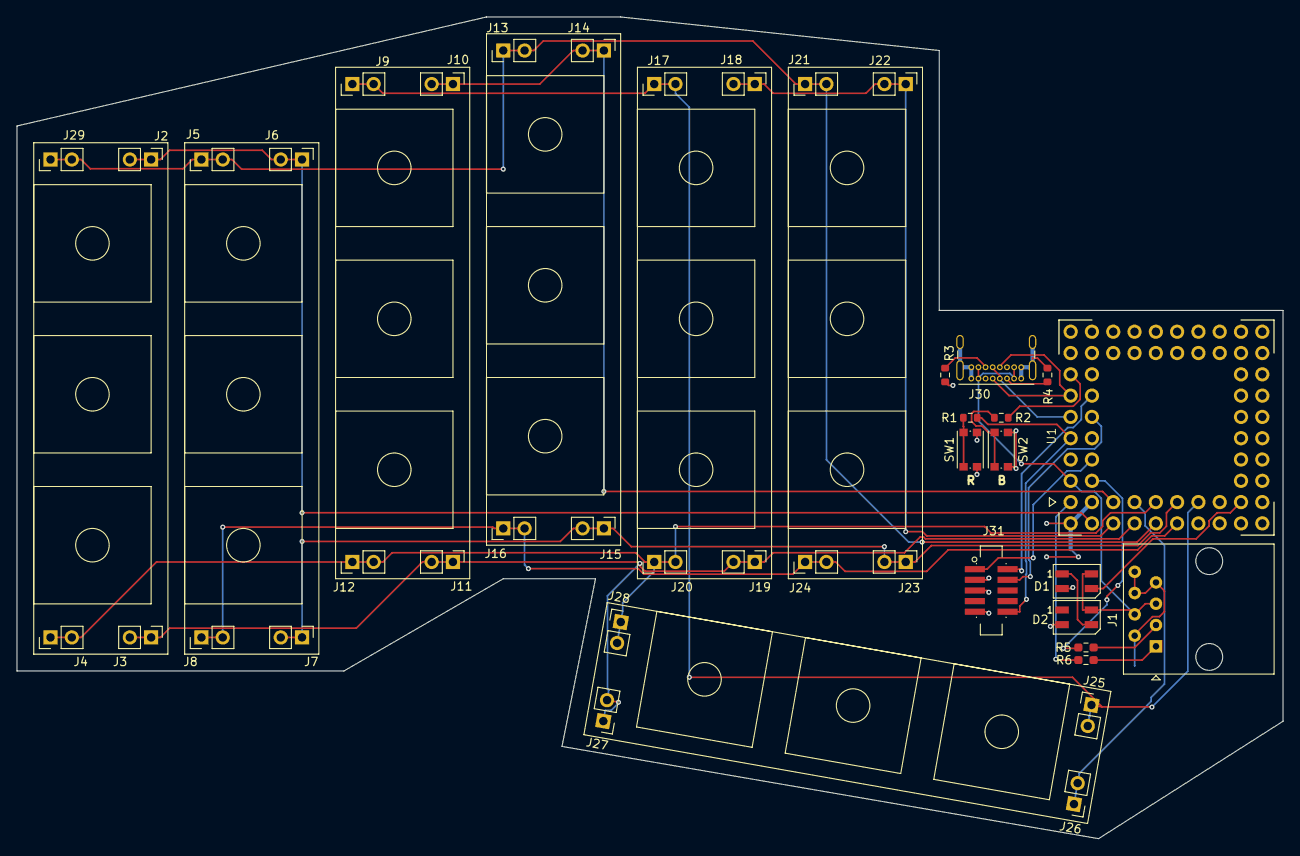
[picture p107: board jolt2-pim-left.kicad_pcb from above]

Board: 2 copper layers, 151.0 x 98.0 mm, 42 parts (0 on the bottom side), 29 nets.

Parts:
D1, D2: SK6812MINI; LED_SK6812MINI_PLCC4_3.5x3.5mm_P1.75mm
J1: RJ45; RJ45_Amphenol_54602-x08_Horizontal
J2, J3, J4, J5, J6, J7, J8, J9, J10, J11, J12, J13, J14, J15, J16, J17, J18, J19, J20, J21, J22, J23, J24, J25, J26, J27, J28, J29: Conn_01x02_Pin; PinHeader_1x02_P2.54mm_Vertical
J30: USB_C_Receptacle_USB2.0_14P; USB_C_Receptacle_GCT_USB4085
J31: Conn_ARM_JTAG_SWD_10; Cortex-M-Debug10
R1, R2: 1k; R_0603_1608Metric
R3, R4: 5.1k; R_0603_1608Metric
R5, R6: 27; R_0603_1608Metric_Pad0.98x0.95mm_HandSolder
SW1, SW2: SW_SPST; SW_Push_1P1T_NO_CK_KMR2
U1: PIMORONI-PGA2035-PM722

Connections:
+3.3V: J31.1 (VTref), U1.3V3
/BOOTSEL: R2.2, U1.BS (BOOTSEL)
/COL-A: J2.1, J2.2, J6.1, J6.2, U1.2 (GP2)
/COL-B: J10.1, J10.2, J14.1, J14.2, U1.3 (GP3)
/COL-C: J18.1, J18.2, J22.1, J22.2, U1.4 (GP4)
/COL-D: J26.1, J26.2, U1.5 (GP5)
/ROW-A: J3.1, J3.2, J11.1, J11.2, J19.1, J19.2, J27.1, J27.2, U1.6 (GP6)
/ROW-B: J4.1, J4.2, J12.1, J12.2, J20.1, J20.2, J28.1, J28.2, U1.7 (GP7)
/ROW-C: J5.1, J5.2, J13.1, J13.2, J21.1, J21.2, J29.1, J29.2, U1.8 (GP8)
/ROW-D: J7.1, J7.2, J15.1, J15.2, J23.1, J23.2, U1.9 (GP9)
/ROW-E: J8.1, J8.2, J16.1, J16.2, J24.1, J24.2, U1.10 (GP10)
/ROW-F: J9.1, J9.2, J17.1, J17.2, J25.1, J25.2, U1.11 (GP11)
/USB_D+: J30.A6 (D+), J30.B6 (D+), U1.D+ (USB_DP)
/USB_D-: J30.A7 (D-), J30.B7 (D-), U1.D- (USB_DM)
GND: D1.2 (VSS), D2.2 (VSS), J1.2, J1.6, J1.7, J1.8, J30.A1 (GND), J30.A12 (GND), J30.B1 (GND), J30.B12 (GND), J30.S1 (SHIELD), J31.3 (GND), J31.5 (GND), J31.9 (GNDDetect), R3.2, R4.2, SW1.1 (A), SW2.1 (A), U1.GND1 (GND), U1.GND2 (GND), U1.GND3 (GND), U1.GND4 (GND), U1.GND5 (GND), U1.GND6 (GND)
unnamed: D1.1 (DOUT), D2.3 (DIN)
unnamed: J30.A5 (CC1), R4.1
unnamed: J30.B5 (CC2), R3.1
unnamed: R1.2, SW1.2 (B)
unnamed: R2.1, SW2.2 (B)
unnamed: R5.1, U1.0 (GP0)
unnamed: R6.1, U1.1 (GP1)
RGB: D1.3 (DIN), U1.15 (GP15)
RUN: J31.10 (~RESET), R1.1, U1.RU (RUN)
SERRX: J1.1, R6.2
SERTX: J1.3, R5.2
SWCLK: J31.4 (SWCLK/TCK), U1.SC (SWCLK)
SWDIO: J31.2 (SWDIO/TMS), U1.SD (SWDIO)
VBUS: D1.4 (VDD), D2.4 (VDD), J1.4, J1.5, J30.A4 (VBUS), J30.A9 (VBUS), J30.B4 (VBUS), J30.B9 (VBUS), U1.VB (VBUS)
