tangybbq/keyboard/jolt2/jolt2-verts/jolt2-verts.kicad_pcb

## KiCad design jolt2/jolt2-verts/jolt2-verts.kicad_pcb (2024-12-16)

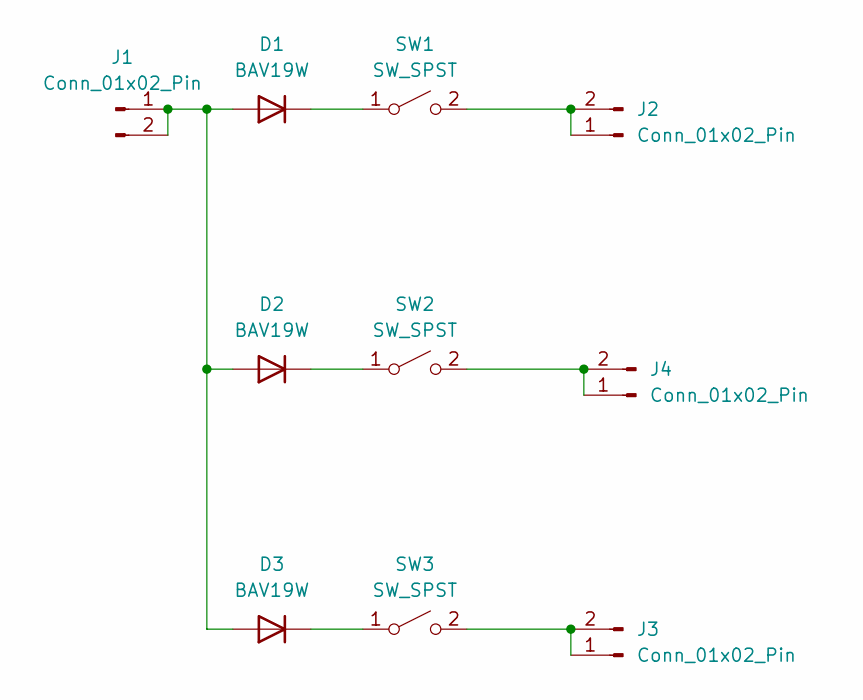
[picture p108: schematic jolt2-verts.kicad_sch, Jolt 2 - Verticals]

Parts:
D1, D2, D3: BAV19W; Nexperia_CFP3_SOD-123W
J1, J2, J3, J4: Conn_01x02_Pin; PinHeader_1x02_P2.54mm_Vertical
SW1, SW2, SW3: SW_SPST; Kailh_socket_PG1350

Connections:
unnamed: D1.2 (A), D2.2 (A), D3.2 (A), J1.1, J1.2
unnamed: D1.1 (K), SW1.1 (A)
unnamed: D2.1 (K), SW2.1 (A)
unnamed: D3.1 (K), SW3.1 (A)
unnamed: J2.1, J2.2, SW1.2 (B)
unnamed: J3.1, J3.2, SW3.2 (B)
unnamed: J4.1, J4.2, SW2.2 (B)

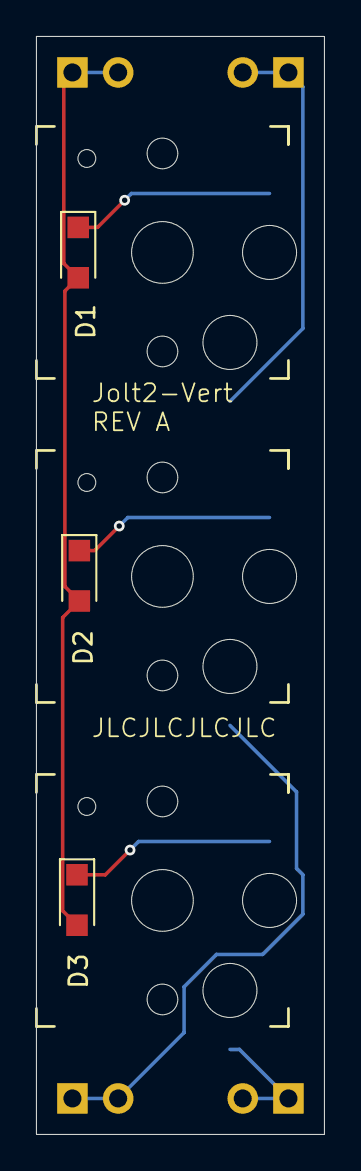
[picture p109: board jolt2-verts.kicad_pcb from above]

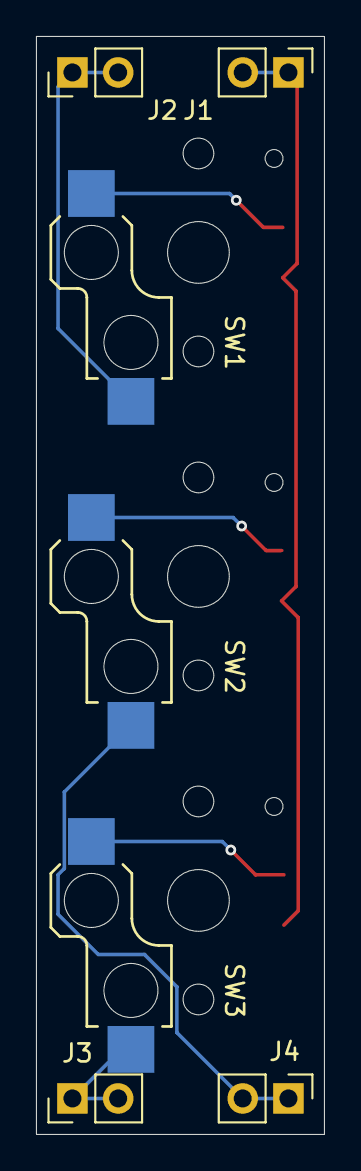
[picture p110: board jolt2-verts.kicad_pcb from below]

Board: 2 copper layers, 16.0 x 61.0 mm, 10 parts (4 on the bottom side), 7 nets.
