tangybbq/keyboard/shield-kb1/shield-kb1.kicad_pcb

## KiCad design shield-kb1/shield-kb1.kicad_pcb (2024-12-16)

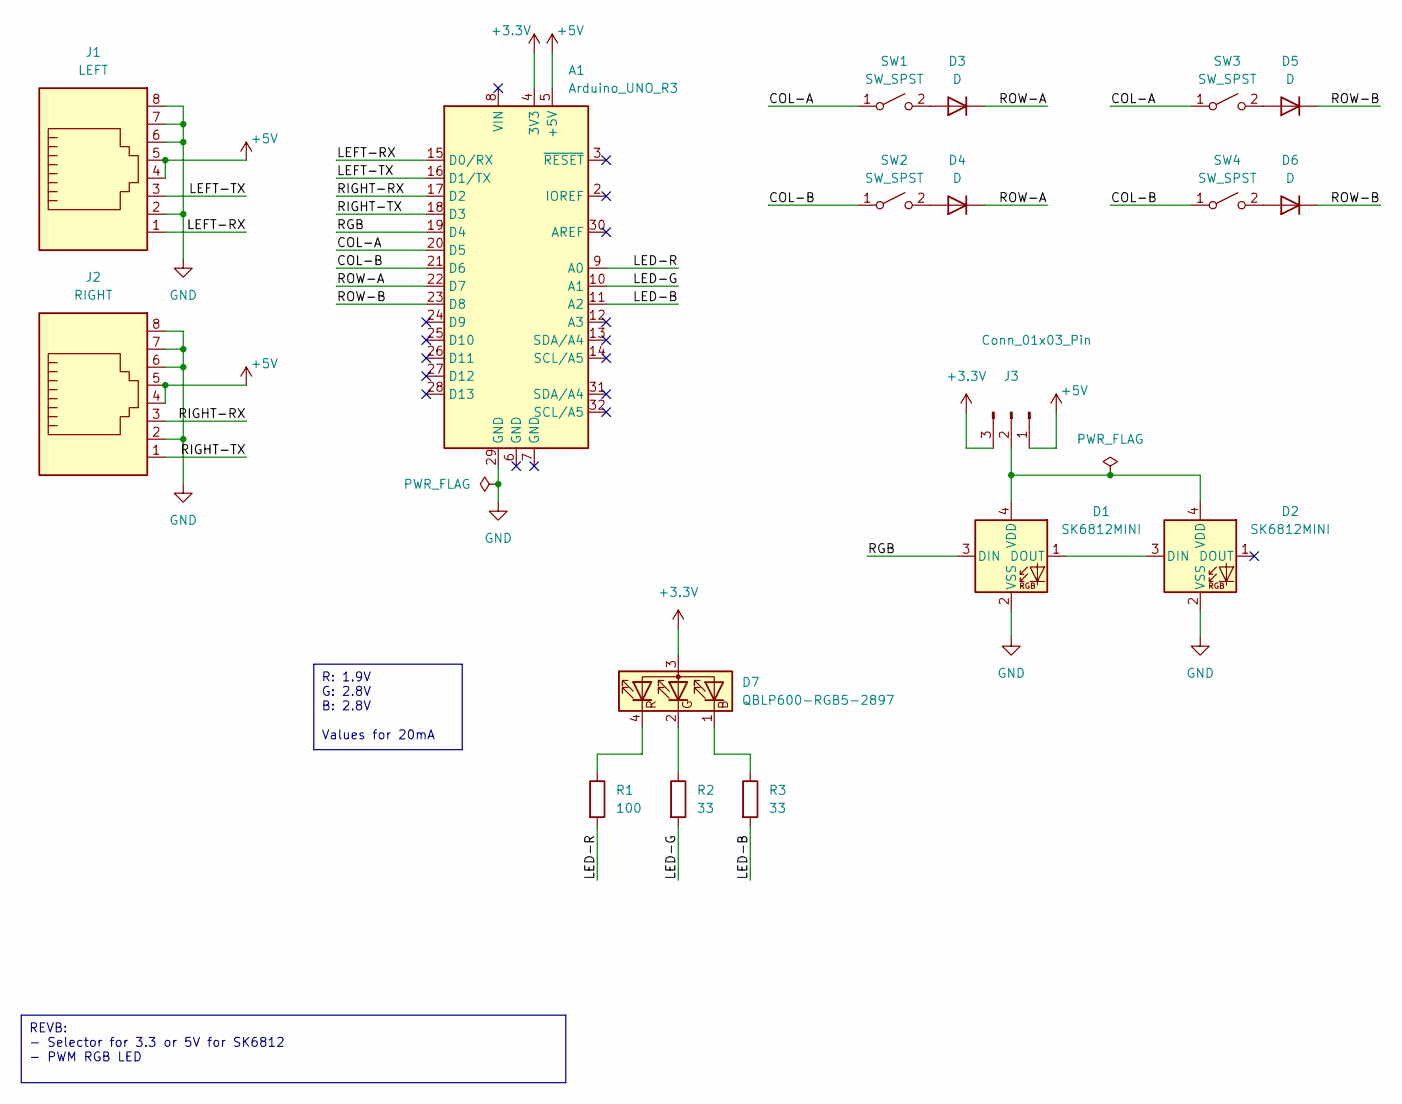
[picture p111: schematic shield-kb1.kicad_sch, Shield KB1]

Parts:
A1: Arduino_UNO_R3
D1, D2: SK6812MINI; LED_SK6812MINI_PLCC4_3.5x3.5mm_P1.75mm
D3, D4, D5, D6: D; Nexperia_CFP3_SOD-123W
D7: QBLP600-RGB5-2897
J1: LEFT; RJ45_Amphenol_54602-x08_Horizontal
J2: RIGHT; RJ45_Amphenol_54602-x08_Horizontal
J3: Conn_01x03_Pin; PinHeader_1x03_P2.54mm_Vertical
R1: 100; R_0603_1608Metric_Pad0.98x0.95mm_HandSolder
R2, R3: 33; R_0603_1608Metric_Pad0.98x0.95mm_HandSolder
SW1, SW2, SW3, SW4: SW_SPST; Kailh_socket_PG1350

Connections:
+3.3V: A1.4 (3V3), D7.3 (A), J3.3
+5V: A1.5 (+5V), J1.4, J1.5, J2.4, J2.5, J3.1
/COL-A: A1.20 (D5), SW1.1 (A), SW3.1 (A)
/COL-B: A1.21 (D6), SW2.1 (A), SW4.1 (A)
/LED-B: A1.11 (A2), R3.2
/LED-G: A1.10 (A1), R2.2
/LED-R: A1.9 (A0), R1.2
/LEFT-RX: A1.15 (D0/RX), J1.1
/LEFT-TX: A1.16 (D1/TX), J1.3
/RGB: A1.19 (D4), D1.3 (DIN)
/RIGHT-RX: A1.17 (D2), J2.3
/RIGHT-TX: A1.18 (D3), J2.1
/ROW-A: A1.22 (D7), D3.1 (K), D4.1 (K)
/ROW-B: A1.23 (D8), D5.1 (K), D6.1 (K)
GND: A1.29 (GND), D1.2 (VSS), D2.2 (VSS), J1.2, J1.6, J1.7, J1.8, J2.2, J2.6, J2.7, J2.8
unnamed: D1.1 (DOUT), D2.3 (DIN)
unnamed: D1.4 (VDD), D2.4 (VDD), J3.2
unnamed: D3.2 (A), SW1.2 (B)
unnamed: D4.2 (A), SW2.2 (B)
unnamed: D5.2 (A), SW3.2 (B)
unnamed: D6.2 (A), SW4.2 (B)
unnamed: D7.1 (BK), R3.1
unnamed: D7.2 (GK), R2.1
unnamed: D7.4 (RK), R1.1

Notes on the sheet:
REVB: - Selector for 3.3 or 5V for SK6812 - PWM RGB LED
R: 1.9V G: 2.8V B: 2.8V Values for 20mA

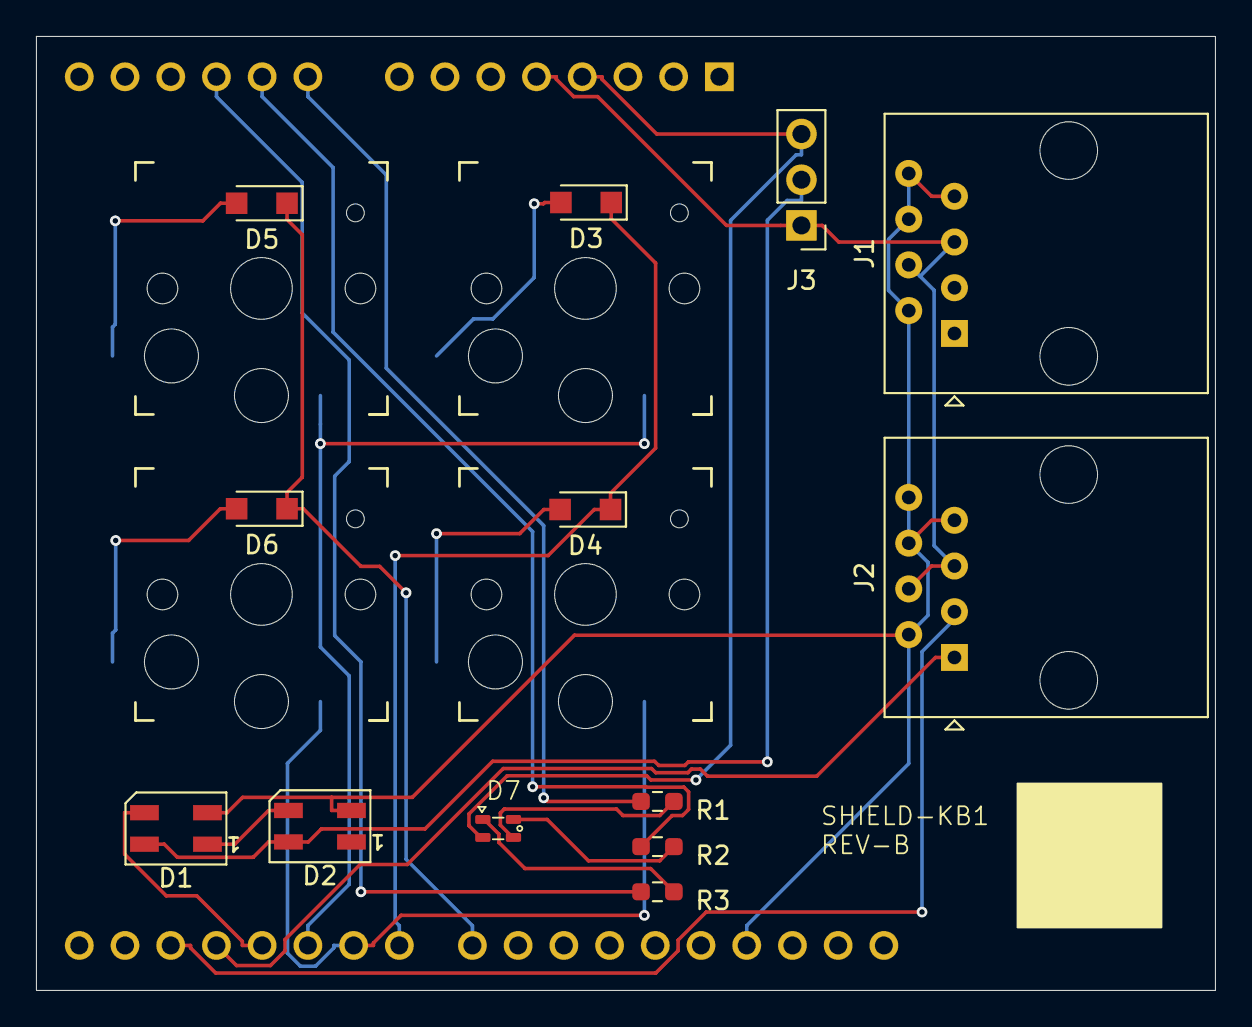
[picture p112: board shield-kb1.kicad_pcb from above]

Board: 2 copper layers, 65.5 x 53.0 mm, 18 parts (1 on the bottom side), 24 nets.
