tangybbq/keyboard/bletest-2/bletest-2.kicad_pcb

## KiCad design bletest-2/bletest-2.kicad_pcb (2024-12-16)

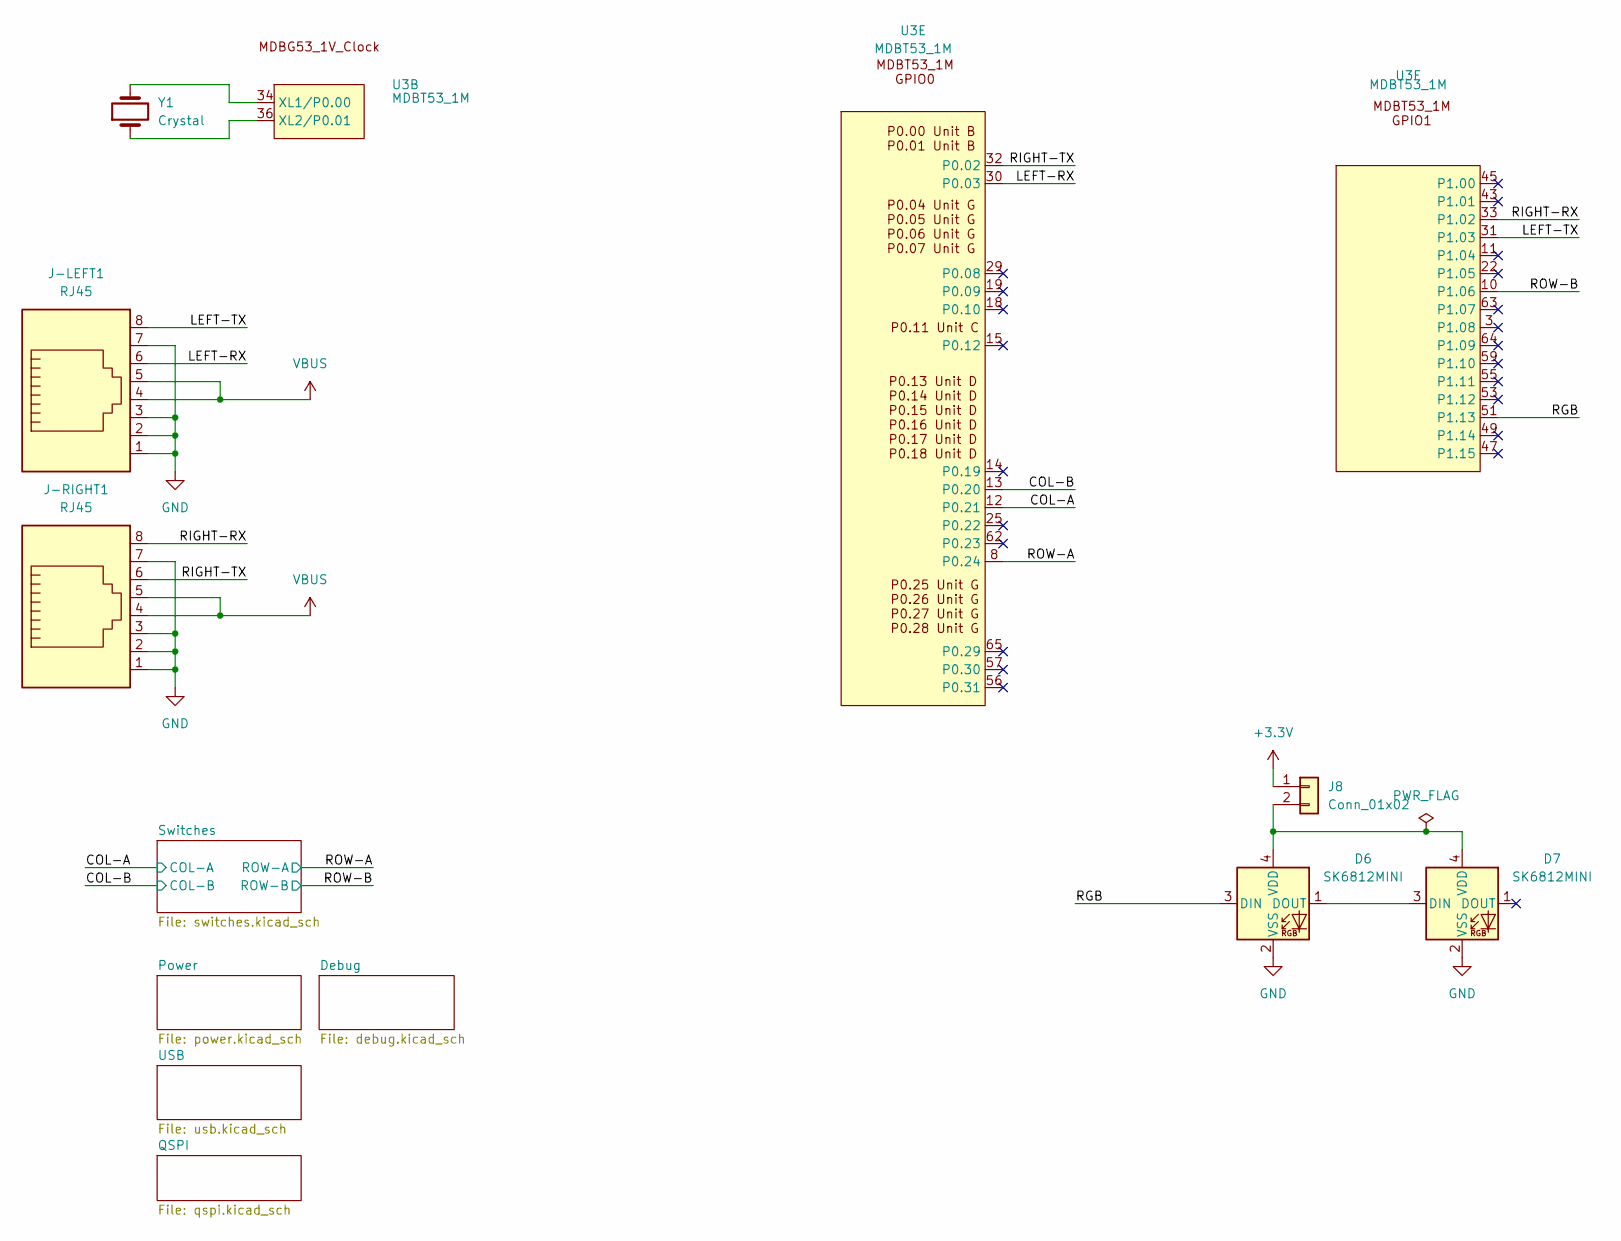
[picture p113: schematic bletest-2.kicad_sch, BLETEXT-2]

Parts:
D6, D7: SK6812MINI; LED_SK6812MINI_PLCC4_3.5x3.5mm_P1.75mm
J8: Conn_01x02; PinHeader_1x02_P2.54mm_Vertical
J-LEFT1: RJ45; RJ45_Amphenol_54602-x08_Horizontal
J-RIGHT1: RJ45; RJ45_Amphenol_54602-x08_Horizontal
U3: MDBT53_1M
Y1: Crystal; Crystal_SMD_3215-2Pin_3.2x1.5mm

Connections:
+3.3V: J8.1; also elsewhere on the board
/COL-A: U3.12 (P0.21); also elsewhere on the board
/COL-B: U3.13 (P0.20); also elsewhere on the board
/LEFT-RX: J-LEFT1.6, U3.30 (P0.03)
/LEFT-TX: J-LEFT1.8, U3.31 (P1.03)
/RGB: D6.3 (DIN), U3.51 (P1.13)
/RIGHT-RX: J-RIGHT1.8, U3.33 (P1.02)
/RIGHT-TX: J-RIGHT1.6, U3.32 (P0.02)
/ROW-A: U3.8 (P0.24); also elsewhere on the board
/ROW-B: U3.10 (P1.06); also elsewhere on the board
GND: D6.2 (VSS), D7.2 (VSS), J-LEFT1.1, J-LEFT1.2, J-LEFT1.3, J-LEFT1.7, J-RIGHT1.1, J-RIGHT1.2, J-RIGHT1.3, J-RIGHT1.7; also elsewhere on the board
unnamed: D6.1 (DOUT), D7.3 (DIN)
unnamed: D6.4 (VDD), D7.4 (VDD), J8.2
unnamed: U3.34 (XL1/P0.00), Y1.2
unnamed: U3.36 (XL2/P0.01), Y1.1
VBUS: J-LEFT1.4, J-LEFT1.5, J-RIGHT1.4, J-RIGHT1.5; also elsewhere on the board

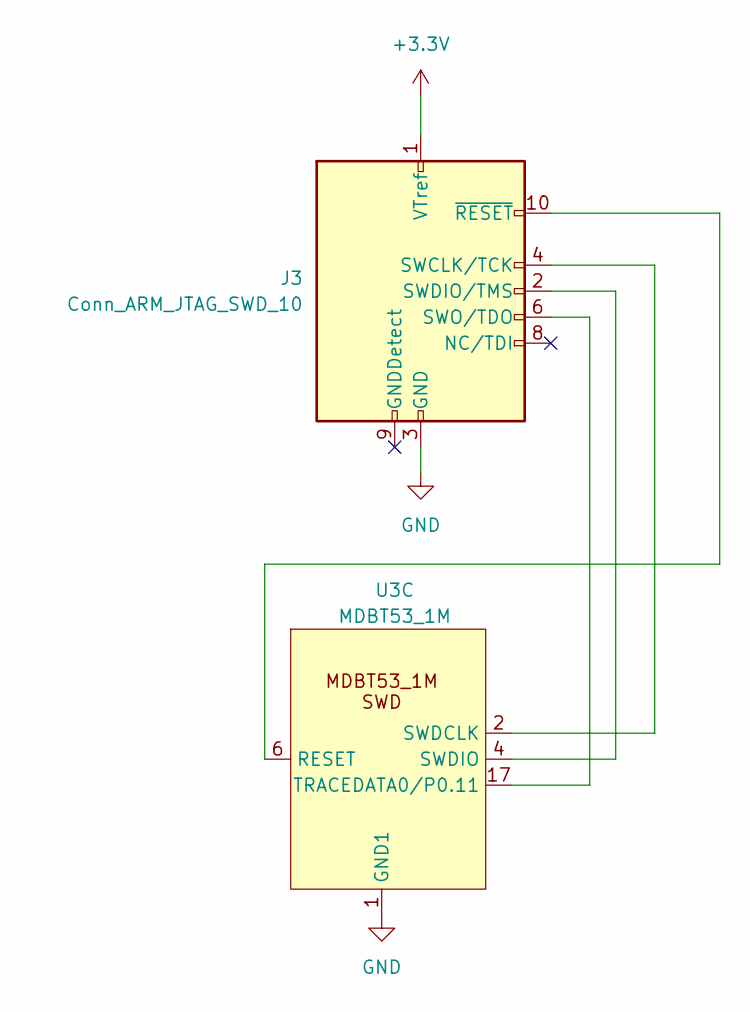
[picture p114: schematic debug.kicad_sch, BLETEXT-2]

Parts:
J3: Conn_ARM_JTAG_SWD_10; Cortex-M-Debug10
U3: MDBT53_1M

Connections:
+3.3V: J3.1 (VTref); also elsewhere on the board
GND: J3.3 (GND), J3.5 (GND), U3.1 (GND1); also elsewhere on the board
unnamed: J3.4 (SWCLK/TCK), U3.2 (SWDCLK)
unnamed: J3.2 (SWDIO/TMS), U3.4 (SWDIO)
unnamed: J3.6 (SWO/TDO), U3.17 (TRACEDATA0/P0.11)
unnamed: J3.10 (~RESET), U3.6 (RESET)

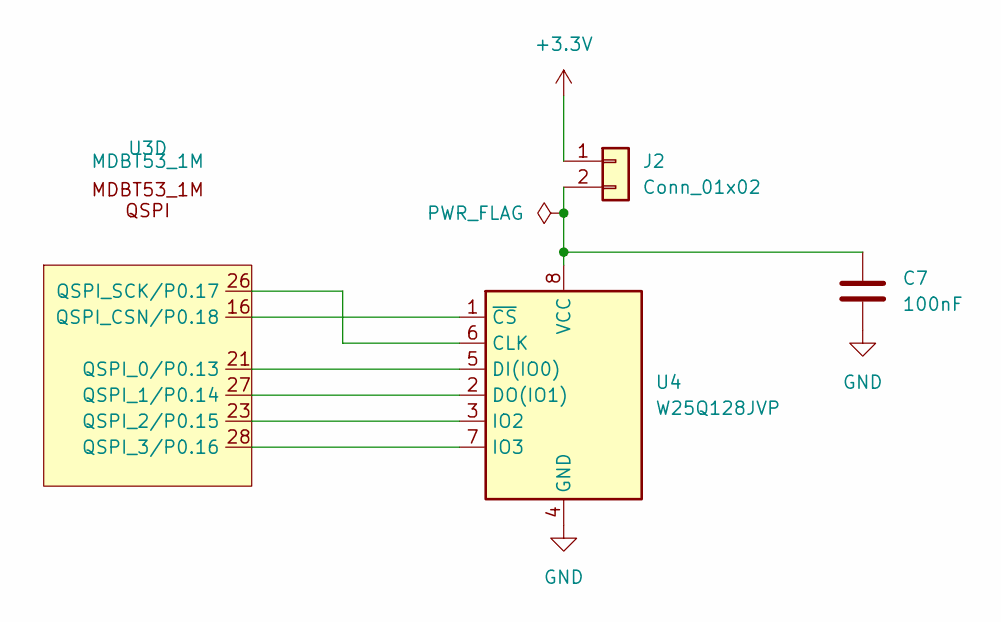
[picture p115: schematic qspi.kicad_sch, BLETEXT-2]

Parts:
C7: 100nF; C_0603_1608Metric
J2: Conn_01x02; PinHeader_1x02_P2.54mm_Vertical
U3: MDBT53_1M
U4: W25Q128JVP; WSON-8-1EP_6x5mm_P1.27mm_EP3.4x4.3mm

Connections:
+3.3V: J2.1; also elsewhere on the board
GND: C7.2, U4.4 (GND); also elsewhere on the board
unnamed: C7.1, J2.2, U4.8 (VCC)
unnamed: U3.21 (QSPI_0/P0.13), U4.5 (DI(IO0))
unnamed: U3.27 (QSPI_1/P0.14), U4.2 (DO(IO1))
unnamed: U3.23 (QSPI_2/P0.15), U4.3 (IO2)
unnamed: U3.28 (QSPI_3/P0.16), U4.7 (IO3)
unnamed: U3.16 (QSPI_CSN/P0.18), U4.1 (~CS)
unnamed: U3.26 (QSPI_SCK/P0.17), U4.6 (CLK)

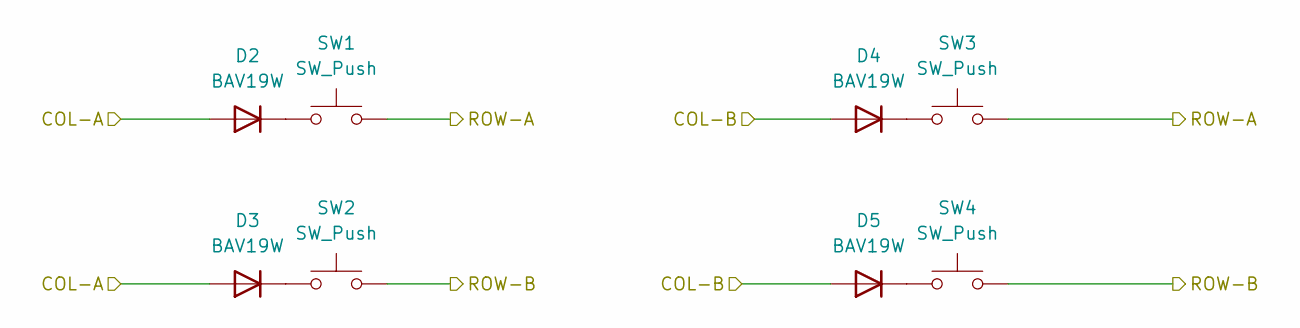
[picture p116: schematic switches.kicad_sch, BLETEXT-2]

Parts:
D2, D3, D4, D5: BAV19W; Nexperia_CFP3_SOD-123W
SW1, SW2, SW3, SW4: SW_Push; Kailh_socket_PG1350

Connections:
/COL-A: D2.2 (A), D3.2 (A); also elsewhere on the board
/COL-B: D4.2 (A), D5.2 (A); also elsewhere on the board
/ROW-A: SW1.2, SW3.2; also elsewhere on the board
/ROW-B: SW2.2, SW4.2; also elsewhere on the board
unnamed: D2.1 (K), SW1.1
unnamed: D3.1 (K), SW2.1
unnamed: D4.1 (K), SW3.1
unnamed: D5.1 (K), SW4.1

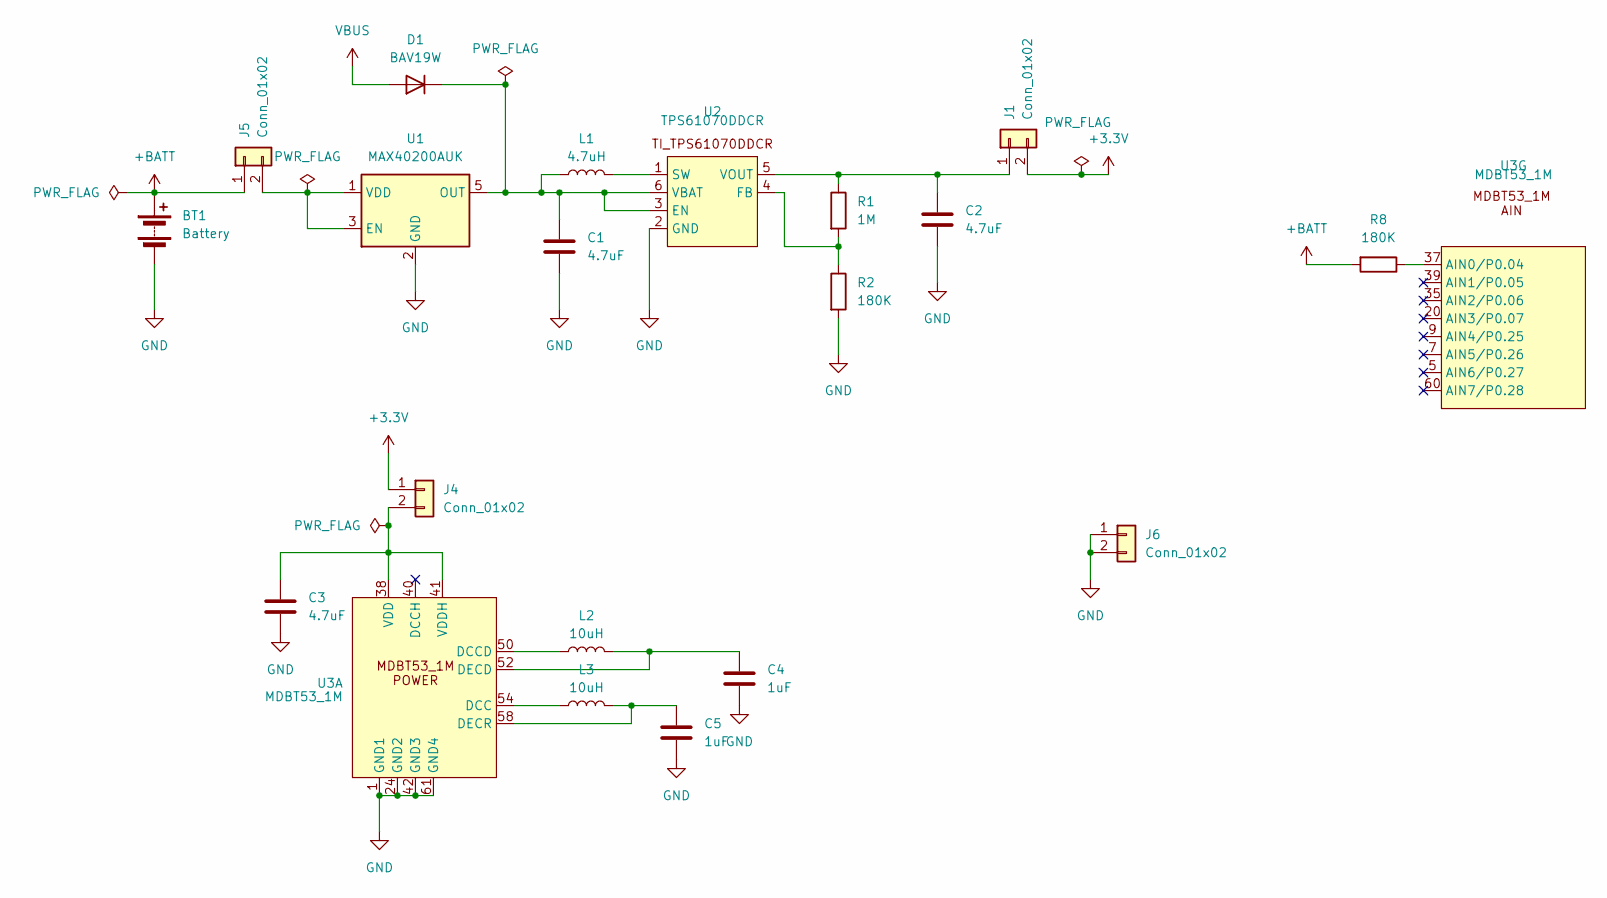
[picture p117: schematic power.kicad_sch, BLETEXT-2]

Parts:
BT1: Battery; BAT-2xAA-SHELL-CASE-BOX-NOSCREW
C1, C2, C3: 4.7uF; C_0603_1608Metric
C4, C5: 1uF; C_0603_1608Metric
D1: BAV19W; Nexperia_CFP3_SOD-123W
J1, J4, J5, J6: Conn_01x02; PinHeader_1x02_P2.54mm_Vertical
L1: 4.7uH; L_0805_2012Metric
L2, L3: 10uH; L_0805_2012Metric
R1: 1M; R_0603_1608Metric
R2, R8: 180K; R_0603_1608Metric
U1: MAX40200AUK; SOT-23-5
U2: TPS61070DDCR; SOT-23-6
U3: MDBT53_1M

Connections:
+3.3V: J1.2, J4.1; also elsewhere on the board
+BATT: BT1.1 (+), J5.1, R8.2
GND: BT1.2 (-), C1.2, C2.2, C3.2, C4.2, C5.2, J6.1, J6.2, R2.2, U1.2 (GND), U2.2 (GND), U3.1 (GND1), U3.24 (GND2), U3.42 (GND3), U3.61 (GND4); also elsewhere on the board
unnamed: C1.1, D1.1 (K), L1.1, U1.5 (OUT), U2.3 (EN), U2.6 (VBAT)
unnamed: C2.1, J1.1, R1.1, U2.5 (VOUT)
unnamed: C3.1, J4.2, U3.38 (VDD), U3.41 (VDDH)
unnamed: J5.2, U1.1 (VDD), U1.3 (EN)
unnamed: R1.2, R2.1, U2.4 (FB)
unnamed: L1.2, U2.1 (SW)
unnamed: L3.1, U3.54 (DCC)
unnamed: L2.1, U3.50 (DCCD)
unnamed: C4.1, L2.2, U3.52 (DECD)
unnamed: C5.1, L3.2, U3.58 (DECR)
unnamed: R8.1, U3.37 (AIN0/P0.04)
VBUS: D1.2 (A); also elsewhere on the board

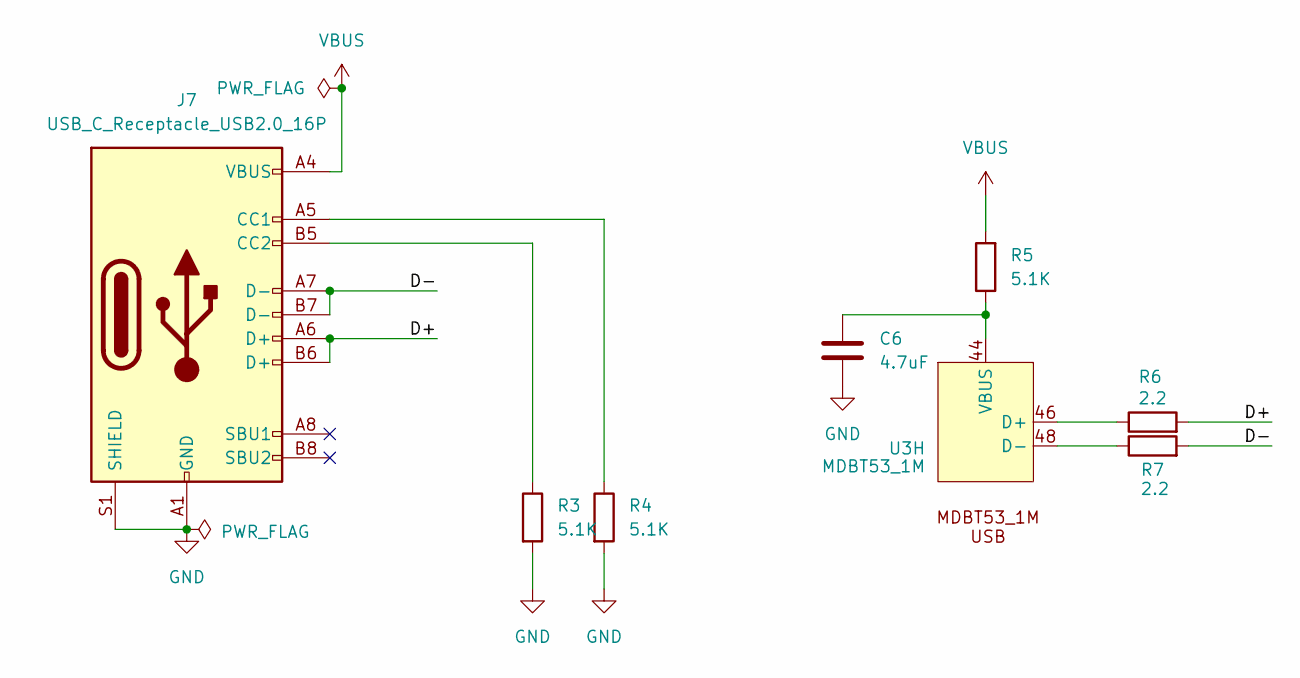
[picture p118: schematic usb.kicad_sch, BLETEXT-2]

Parts:
C6: 4.7uF; C_0603_1608Metric
J7: USB_C_Receptacle_USB2.0_16P; USB_C_Receptacle_GCT_USB4085
R3, R4, R5: 5.1K; R_0603_1608Metric
R6, R7: 2.2; R_0603_1608Metric
U3: MDBT53_1M

Connections:
/USB/D+: J7.A6 (D+), J7.B6 (D+), R6.2
/USB/D-: J7.A7 (D-), J7.B7 (D-), R7.2
GND: C6.2, J7.A1 (GND), J7.A12 (GND), J7.B1 (GND), J7.B12 (GND), J7.S1 (SHIELD), R3.2, R4.2; also elsewhere on the board
unnamed: J7.A5 (CC1), R4.1
unnamed: J7.B5 (CC2), R3.1
unnamed: R6.1, U3.46 (D+)
unnamed: R7.1, U3.48 (D-)
unnamed: C6.1, R5.1, U3.44 (VBUS)
VBUS: J7.A4 (VBUS), J7.A9 (VBUS), J7.B4 (VBUS), J7.B9 (VBUS), R5.2; also elsewhere on the board

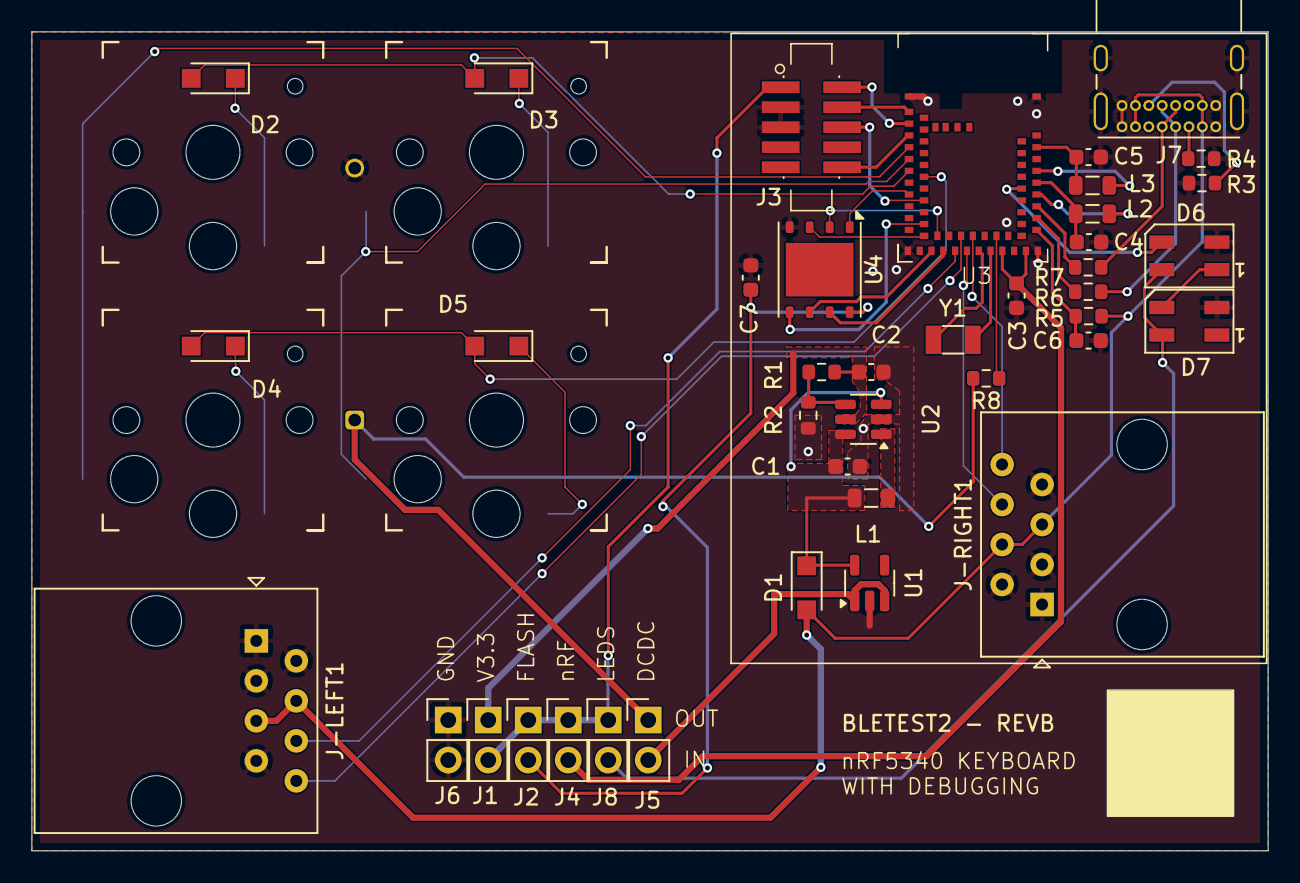
[picture p119: board bletest-2.kicad_pcb from above]

Board: 2 copper layers, 78.5 x 52.0 mm, 45 parts (1 on the bottom side), 50 nets.
